cxdzyq1110/posture_recognition_CNN/projects/matlab/hog_svm/man+bike.png

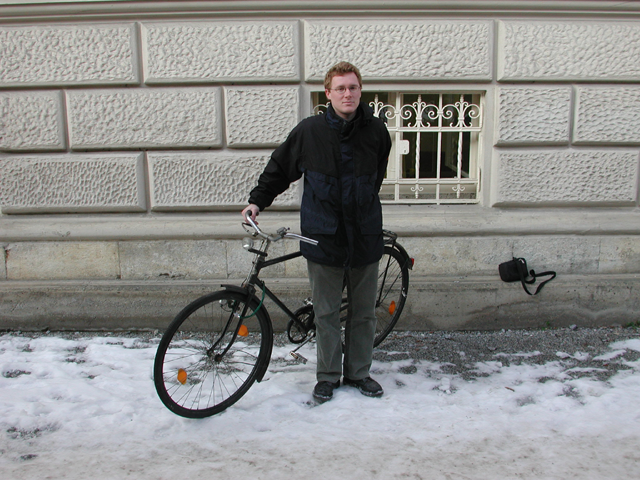
projects/matlab/hog_svm/man+bike.png
