cxdzyq1110/posture_recognition_CNN/projects/matlab/picture/wangjunkai/1.jpg

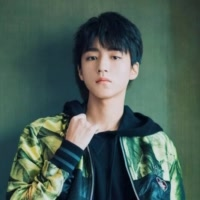
projects/matlab/picture/wangjunkai/1.jpg
