cxdzyq1110/posture_recognition_CNN/projects/zFPGA_DE10_NANO_SoC/01_altera_ip/soc_system/soc_system/synthesis/submodules/soc_system_mm_interconnect_0_router.sv

// (C) 2001-2014 Altera Corporation. All rights reserved.
// Your use of Altera Corporation's design tools, logic functions and other 
// software and tools, and its AMPP partner logic functions, and any output 
// files any of the foregoing (including device programming or simulation 
// files), and any associated documentation or information are expressly subject 
// to the terms and conditions of the Altera Program License Subscription 
// Agreement, Altera MegaCore Function License Agreement, or other applicable 
// license agreement, including, without limitation, that your use is for the 
// sole purpose of programming logic devices manufactured by Altera and sold by 
// Altera or its authorized distributors.  Please refer to the applicable 
// agreement for further details.



// Your use of Altera Corporation's design tools, logic functions and other 
// software and tools, and its AMPP partner logic functions, and any output 
// files any of the foregoing (including device programming or simulation 
// files), and any associated documentation or information are expressly subject 
// to the terms and conditions of the Altera Program License Subscription 
// Agreement, Altera MegaCore Function License Agreement, or other applicable 
// license agreement, including, without limitation, that your use is for the 
// sole purpose of programming logic devices manufactured by Altera and sold by 
// Altera or its authorized distributors.  Please refer to the applicable 
// agreement for further details.


// $Id: //acds/rel/14.0/ip/merlin/altera_merlin_router/altera_merlin_router.sv.terp#1 $
// $Revision: #1 $
// $Date: 2014/02/16 $
// $Author: swbranch $

// -------------------------------------------------------
// Merlin Router
//
// Asserts the appropriate one-hot encoded channel based on 
// either (a) the address or (b) the dest id. The DECODER_TYPE
// parameter controls this behaviour. 0 means address decoder,
// 1 means dest id decoder.
//
// In the case of (a), it also sets the destination id.
// -------------------------------------------------------

`timescale 1 ns / 1 ns

module soc_system_mm_interconnect_0_router_default_decode
  #(
     parameter DEFAULT_CHANNEL = 2,
               DEFAULT_WR_CHANNEL = -1,
               DEFAULT_RD_CHANNEL = -1,
               DEFAULT_DESTID = 0 
   )
  (output [91 - 89 : 0] default_destination_id,
   output [8-1 : 0] default_wr_channel,
   output [8-1 : 0] default_rd_channel,
   output [8-1 : 0] default_src_channel
  );

  assign default_destination_id = 
    DEFAULT_DESTID[91 - 89 : 0];

  generate begin : default_decode
    if (DEFAULT_CHANNEL == -1) begin
      assign default_src_channel = '0;
    end
    else begin
      assign default_src_channel = 8'b1 << DEFAULT_CHANNEL;
    end
  end
  endgenerate

  generate begin : default_decode_rw
    if (DEFAULT_RD_CHANNEL == -1) begin
      assign default_wr_channel = '0;
      assign default_rd_channel = '0;
    end
    else begin
      assign default_wr_channel = 8'b1 << DEFAULT_WR_CHANNEL;
      assign default_rd_channel = 8'b1 << DEFAULT_RD_CHANNEL;
    end
  end
  endgenerate

endmodule


module soc_system_mm_interconnect_0_router
(
    // -------------------
    // Clock & Reset
    // -------------------
    input clk,
    input reset,

    // -------------------
    // Command Sink (Input)
    // -------------------
    input                       sink_valid,
    input  [116-1 : 0]    sink_data,
    input                       sink_startofpacket,
    input                       sink_endofpacket,
    output                      sink_ready,

    // -------------------
    // Command Source (Output)
    // -------------------
    output                          src_valid,
    output reg [116-1    : 0] src_data,
    output reg [8-1 : 0] src_channel,
    output                          src_startofpacket,
    output                          src_endofpacket,
    input                           src_ready
);

    // -------------------------------------------------------
    // Local parameters and variables
    // -------------------------------------------------------
    localparam PKT_ADDR_H = 56;
    localparam PKT_ADDR_L = 36;
    localparam PKT_DEST_ID_H = 91;
    localparam PKT_DEST_ID_L = 89;
    localparam PKT_PROTECTION_H = 106;
    localparam PKT_PROTECTION_L = 104;
    localparam ST_DATA_W = 116;
    localparam ST_CHANNEL_W = 8;
    localparam DECODER_TYPE = 0;

    localparam PKT_TRANS_WRITE = 59;
    localparam PKT_TRANS_READ  = 60;

    localparam PKT_ADDR_W = PKT_ADDR_H-PKT_ADDR_L + 1;
    localparam PKT_DEST_ID_W = PKT_DEST_ID_H-PKT_DEST_ID_L + 1;



    // -------------------------------------------------------
    // Figure out the number of bits to mask off for each slave span
    // during address decoding
    // -------------------------------------------------------
    localparam PAD0 = log2ceil(64'h10000 - 64'h0); 
    localparam PAD1 = log2ceil(64'h40018 - 64'h40010); 
    localparam PAD2 = log2ceil(64'h40030 - 64'h40020); 
    localparam PAD3 = log2ceil(64'h41010 - 64'h41000); 
    localparam PAD4 = log2ceil(64'h42010 - 64'h42000); 
    localparam PAD5 = log2ceil(64'h43010 - 64'h43000); 
    localparam PAD6 = log2ceil(64'h44010 - 64'h44000); 
    localparam PAD7 = log2ceil(64'h49000 - 64'h48000); 
    // -------------------------------------------------------
    // Work out which address bits are significant based on the
    // address range of the slaves. If the required width is too
    // large or too small, we use the address field width instead.
    // -------------------------------------------------------
    localparam ADDR_RANGE = 64'h49000;
    localparam RANGE_ADDR_WIDTH = log2ceil(ADDR_RANGE);
    localparam OPTIMIZED_ADDR_H = (RANGE_ADDR_WIDTH > PKT_ADDR_W) ||
                                  (RANGE_ADDR_WIDTH == 0) ?
                                        PKT_ADDR_H :
                                        PKT_ADDR_L + RANGE_ADDR_WIDTH - 1;

    localparam RG = RANGE_ADDR_WIDTH-1;
    localparam REAL_ADDRESS_RANGE = OPTIMIZED_ADDR_H - PKT_ADDR_L;

      reg [PKT_ADDR_W-1 : 0] address;
      always @* begin
        address = {PKT_ADDR_W{1'b0}};
        address [REAL_ADDRESS_RANGE:0] = sink_data[OPTIMIZED_ADDR_H : PKT_ADDR_L];
      end   

    // -------------------------------------------------------
    // Pass almost everything through, untouched
    // -------------------------------------------------------
    assign sink_ready        = src_ready;
    assign src_valid         = sink_valid;
    assign src_startofpacket = sink_startofpacket;
    assign src_endofpacket   = sink_endofpacket;
    wire [PKT_DEST_ID_W-1:0] default_destid;
    wire [8-1 : 0] default_src_channel;




    // -------------------------------------------------------
    // Write and read transaction signals
    // -------------------------------------------------------
    wire read_transaction;
    assign read_transaction  = sink_data[PKT_TRANS_READ];


    soc_system_mm_interconnect_0_router_default_decode the_default_decode(
      .default_destination_id (default_destid),
      .default_wr_channel   (),
      .default_rd_channel   (),
      .default_src_channel  (default_src_channel)
    );

    always @* begin
        src_data    = sink_data;
        src_channel = default_src_channel;
        src_data[PKT_DEST_ID_H:PKT_DEST_ID_L] = default_destid;

        // --------------------------------------------------
        // Address Decoder
        // Sets the channel and destination ID based on the address
        // --------------------------------------------------

    // ( 0x0 .. 0x10000 )
    if ( {address[RG:PAD0],{PAD0{1'b0}}} == 19'h0   ) begin
            src_channel = 8'b00000100;
            src_data[PKT_DEST_ID_H:PKT_DEST_ID_L] = 0;
    end

    // ( 0x40010 .. 0x40018 )
    if ( {address[RG:PAD1],{PAD1{1'b0}}} == 19'h40010  && read_transaction  ) begin
            src_channel = 8'b00000001;
            src_data[PKT_DEST_ID_H:PKT_DEST_ID_L] = 6;
    end

    // ( 0x40020 .. 0x40030 )
    if ( {address[RG:PAD2],{PAD2{1'b0}}} == 19'h40020   ) begin
            src_channel = 8'b00000010;
            src_data[PKT_DEST_ID_H:PKT_DEST_ID_L] = 3;
    end

    // ( 0x41000 .. 0x41010 )
    if ( {address[RG:PAD3],{PAD3{1'b0}}} == 19'h41000   ) begin
            src_channel = 8'b00001000;
            src_data[PKT_DEST_ID_H:PKT_DEST_ID_L] = 2;
    end

    // ( 0x42000 .. 0x42010 )
    if ( {address[RG:PAD4],{PAD4{1'b0}}} == 19'h42000  && read_transaction  ) begin
            src_channel = 8'b00010000;
            src_data[PKT_DEST_ID_H:PKT_DEST_ID_L] = 1;
    end

    // ( 0x43000 .. 0x43010 )
    if ( {address[RG:PAD5],{PAD5{1'b0}}} == 19'h43000  && read_transaction  ) begin
            src_channel = 8'b00100000;
            src_data[PKT_DEST_ID_H:PKT_DEST_ID_L] = 7;
    end

    // ( 0x44000 .. 0x44010 )
    if ( {address[RG:PAD6],{PAD6{1'b0}}} == 19'h44000   ) begin
            src_channel = 8'b01000000;
            src_data[PKT_DEST_ID_H:PKT_DEST_ID_L] = 4;
    end

    // ( 0x48000 .. 0x49000 )
    if ( {address[RG:PAD7],{PAD7{1'b0}}} == 19'h48000   ) begin
            src_channel = 8'b10000000;
            src_data[PKT_DEST_ID_H:PKT_DEST_ID_L] = 5;
    end

end


    // --------------------------------------------------
    // Ceil(log2()) function
    // --------------------------------------------------
    function integer log2ceil;
        input reg[65:0] val;
        reg [65:0] i;

        begin
            i = 1;
            log2ceil = 0;

            while (i < val) begin
                log2ceil = log2ceil + 1;
                i = i << 1;
            end
        end
    endfunction

endmodule
