cxdzyq1110/posture_recognition_CNN/projects/zFPGA_DE10_NANO_SoC/08_quartus/hps_isw_handoff/soc_system_hps_0/sequencer.c

/*
* Copyright Altera Corporation (C) 2012-2014. All rights reserved
*
* SPDX-License-Identifier:  BSD-3-Clause
*
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
* THIS SOFTWARE IS PROVIDED BY THE COPYRIGHT HOLDERS AND CONTRIBUTORS "AS IS" AND
* ANY EXPRESS OR IMPLIED WARRANTIES, INCLUDING, BUT NOT LIMITED TO, THE IMPLIED
* WARRANTIES OF MERCHANTABILITY AND FITNESS FOR A PARTICULAR PURPOSE ARE
* DISCLAIMED. IN NO EVENT SHALL ALTERA CORPORATION BE LIABLE FOR ANY
* DIRECT, INDIRECT, INCIDENTAL, SPECIAL, EXEMPLARY, OR CONSEQUENTIAL DAMAGES
* (INCLUDING, BUT NOT LIMITED TO, PROCUREMENT OF SUBSTITUTE GOODS OR SERVICES;
* LOSS OF USE, DATA, OR PROFITS; OR BUSINESS INTERRUPTION) HOWEVER CAUSED AND
* ON ANY THEORY OF LIABILITY, WHETHER IN CONTRACT, STRICT LIABILITY, OR TORT
* (INCLUDING NEGLIGENCE OR OTHERWISE) ARISING IN ANY WAY OUT OF THE USE OF THIS
* SOFTWARE, EVEN IF ADVISED OF THE POSSIBILITY OF SUCH DAMAGE.
*/


#include "sequencer_defines.h"

#include "alt_types.h"
#include "system.h"
#if HPS_HW
#include "sdram_io.h"
#else
#include "io.h"
#endif
#include "sequencer.h"
#include "tclrpt.h"
#include "sequencer_auto.h"

#if HHP_HPS_SIMULATION
#include "hps_controller.h"
#endif


/******************************************************************************
 ******************************************************************************
 ** NOTE: Special Rules for Globale Variables                                **
 **                                                                          **
 ** All global variables that are explicitly initialized (including          **
 ** explicitly initialized to zero), are only initialized once, during       **
 ** configuration time, and not again on reset.  This means that they        **
 ** preserve their current contents across resets, which is needed for some  **
 ** special cases involving communication with external modules.  In         **
 ** addition, this avoids paying the price to have the memory initialized,   **
 ** even for zeroed data, provided it is explicitly set to zero in the code, **
 ** and doesn't rely on implicit initialization.                             **
 ******************************************************************************
 ******************************************************************************/


#if ARRIAV
// Temporary workaround to place the initial stack pointer at a safe offset from end
#define STRINGIFY(s)		STRINGIFY_STR(s)
#define STRINGIFY_STR(s)	#s
asm(".global __alt_stack_pointer");
asm("__alt_stack_pointer = " STRINGIFY(STACK_POINTER));
#endif

#if CYCLONEV
// Temporary workaround to place the initial stack pointer at a safe offset from end
#define STRINGIFY(s)		STRINGIFY_STR(s)
#define STRINGIFY_STR(s)	#s
asm(".global __alt_stack_pointer");
asm("__alt_stack_pointer = " STRINGIFY(STACK_POINTER));
#endif

#if ENABLE_PRINTF_LOG
#include <stdio.h>
#include <string.h>

typedef struct {
	alt_u32 v;
	alt_u32 p;
	alt_u32 d;
	alt_u32 ps;
} dqs_pos_t;

/*
The parameters that were previously here are now supplied by generation, until the new data manager is working.
*/

struct {
	const char *stage;

	alt_u32 vfifo_idx;

	dqs_pos_t gwrite_pos[RW_MGR_MEM_IF_WRITE_DQS_WIDTH];

	dqs_pos_t dqs_enable_left_edge[RW_MGR_MEM_IF_READ_DQS_WIDTH];
	dqs_pos_t dqs_enable_right_edge[RW_MGR_MEM_IF_READ_DQS_WIDTH];
	dqs_pos_t dqs_enable_mid[RW_MGR_MEM_IF_READ_DQS_WIDTH];

	dqs_pos_t dqs_wlevel_left_edge[RW_MGR_MEM_IF_WRITE_DQS_WIDTH];
	dqs_pos_t dqs_wlevel_right_edge[RW_MGR_MEM_IF_WRITE_DQS_WIDTH];
	dqs_pos_t dqs_wlevel_mid[RW_MGR_MEM_IF_WRITE_DQS_WIDTH];

	alt_32 dq_read_left_edge[RW_MGR_MEM_IF_READ_DQS_WIDTH][RW_MGR_MEM_DQ_PER_READ_DQS];
	alt_32 dq_read_right_edge[RW_MGR_MEM_IF_READ_DQS_WIDTH][RW_MGR_MEM_DQ_PER_READ_DQS];
	alt_32 dq_write_left_edge[RW_MGR_MEM_IF_WRITE_DQS_WIDTH][RW_MGR_MEM_DQ_PER_READ_DQS];
	alt_32 dq_write_right_edge[RW_MGR_MEM_IF_WRITE_DQS_WIDTH][RW_MGR_MEM_DQ_PER_READ_DQS];
	alt_32 dm_left_edge[RW_MGR_MEM_IF_WRITE_DQS_WIDTH][RW_MGR_NUM_DM_PER_WRITE_GROUP];
	alt_32 dm_right_edge[RW_MGR_MEM_IF_WRITE_DQS_WIDTH][RW_MGR_NUM_DM_PER_WRITE_GROUP];
} bfm_gbl;

#endif

#if HPS_HW
#include <sdram.h>
#endif // HPS_HW

#if BFM_MODE
#include <stdio.h>

// DPI access function via library
extern long long get_sim_time(void);

typedef struct {
	alt_u32 v;
	alt_u32 p;
	alt_u32 d;
	alt_u32 ps;
} dqs_pos_t;

/*
The parameters that were previously here are now supplied by generation, until the new data manager is working.
*/

struct {
	FILE *outfp;
	int bfm_skip_guaranteed_write;
	int trk_sample_count;
	int trk_long_idle_updates;
	int lfifo_margin;
	const char *stage;

	alt_u32 vfifo_idx;

	dqs_pos_t gwrite_pos[RW_MGR_MEM_IF_WRITE_DQS_WIDTH];
	
	dqs_pos_t dqs_enable_left_edge[RW_MGR_MEM_IF_READ_DQS_WIDTH];
	dqs_pos_t dqs_enable_right_edge[RW_MGR_MEM_IF_READ_DQS_WIDTH];
	dqs_pos_t dqs_enable_mid[RW_MGR_MEM_IF_READ_DQS_WIDTH];

	dqs_pos_t dqs_wlevel_left_edge[RW_MGR_MEM_IF_WRITE_DQS_WIDTH];
	dqs_pos_t dqs_wlevel_right_edge[RW_MGR_MEM_IF_WRITE_DQS_WIDTH];
	dqs_pos_t dqs_wlevel_mid[RW_MGR_MEM_IF_WRITE_DQS_WIDTH];

	alt_32 dq_read_left_edge[RW_MGR_MEM_IF_READ_DQS_WIDTH][RW_MGR_MEM_DQ_PER_READ_DQS];
	alt_32 dq_read_right_edge[RW_MGR_MEM_IF_READ_DQS_WIDTH][RW_MGR_MEM_DQ_PER_READ_DQS];
	alt_32 dq_write_left_edge[RW_MGR_MEM_IF_WRITE_DQS_WIDTH][RW_MGR_MEM_DQ_PER_WRITE_DQS];
	alt_32 dq_write_right_edge[RW_MGR_MEM_IF_WRITE_DQS_WIDTH][RW_MGR_MEM_DQ_PER_WRITE_DQS];
	alt_32 dm_left_edge[RW_MGR_MEM_IF_WRITE_DQS_WIDTH][RW_MGR_NUM_DM_PER_WRITE_GROUP];
	alt_32 dm_right_edge[RW_MGR_MEM_IF_WRITE_DQS_WIDTH][RW_MGR_NUM_DM_PER_WRITE_GROUP];
} bfm_gbl;


#endif

#if ENABLE_TCL_DEBUG
debug_data_t my_debug_data;
#endif

#define NEWVERSION_RDDESKEW 1
#define NEWVERSION_WRDESKEW 1
#define NEWVERSION_GW 1
#define NEWVERSION_WL 1
#define NEWVERSION_DQSEN 1

// Just to make the debugging code more uniform
#ifndef RW_MGR_MEM_NUMBER_OF_CS_PER_DIMM
#define RW_MGR_MEM_NUMBER_OF_CS_PER_DIMM 0
#endif

#if HALF_RATE
#define HALF_RATE_MODE 1
#else
#define HALF_RATE_MODE 0
#endif

#if QUARTER_RATE
#define QUARTER_RATE_MODE 1
#else
#define QUARTER_RATE_MODE 0
#endif
#define DELTA_D 1

// case:56390
// VFIFO_CONTROL_WIDTH_PER_DQS is the number of VFIFOs actually instantiated per DQS. This is always one except:
// AV QDRII where it is 2 for x18 and x18w2, and 4 for x36 and x36w2
// RLDRAMII x36 and x36w2 where it is 2.
// In 12.0sp1 we set this to 4 for all of the special cases above to keep it simple.
// In 12.0sp2 or 12.1 this should get moved to generation and unified with the same constant used in the phy mgr

#define VFIFO_CONTROL_WIDTH_PER_DQS 1

#if ARRIAV

#if QDRII 
 #if RW_MGR_MEM_DQ_PER_READ_DQS > 9
  #undef VFIFO_CONTROL_WIDTH_PER_DQS
  #define VFIFO_CONTROL_WIDTH_PER_DQS 4
 #endif
#endif // protocol check

#if RLDRAMII
 #if RW_MGR_MEM_DQ_PER_READ_DQS > 9
  #undef VFIFO_CONTROL_WIDTH_PER_DQS
  #define VFIFO_CONTROL_WIDTH_PER_DQS 2
 #endif
#endif // protocol check

#endif // family check

// In order to reduce ROM size, most of the selectable calibration steps are
// decided at compile time based on the user's calibration mode selection,
// as captured by the STATIC_CALIB_STEPS selection below.
//
// However, to support simulation-time selection of fast simulation mode, where
// we skip everything except the bare minimum, we need a few of the steps to
// be dynamic.  In those cases, we either use the DYNAMIC_CALIB_STEPS for the
// check, which is based on the rtl-supplied value, or we dynamically compute the
// value to use based on the dynamically-chosen calibration mode

#if QDRII
#define BTFLD_FMT "%llx"
#else
#define BTFLD_FMT "%lx"
#endif

#if BFM_MODE // ~~~~~~~~~~~~~~~~~~~~~~~~~~~~~~~~~~~~~~~~~~~~~~~~~~~~~~~~~~~~~~~~~~~~~~~~


// TODO: should make this configurable; could even have it read from config file or env at startup
#define DLEVEL 2
// space around comma is required for varargs macro to remove comma if args is empty
#define DPRINT(level, fmt, args...) 	if (DLEVEL >= (level)) printf("[%lld] SEQ.C: " fmt "\n" , get_sim_time(), ## args)
#define IPRINT(fmt, args...) 	printf("[%lld] SEQ.C: " fmt "\n" , get_sim_time(), ## args)
#define BFM_GBL_SET(field,value)	bfm_gbl.field = value
#define BFM_GBL_GET(field)		bfm_gbl.field
#define BFM_STAGE(label)		BFM_GBL_SET(stage,label)
#define BFM_INC_VFIFO			bfm_gbl.vfifo_idx = (bfm_gbl.vfifo_idx + 1) % VFIFO_SIZE
#define COV(label)			getpid() /* no-op marker for coverage */

#elif ENABLE_PRINTF_LOG // ~~~~~~~~~~~~~~~~~~~~~~~~~~~~~~~~~~~~~~~~~~~~~~~~~~~~~~~~~~~~~~

#define DLEVEL 2

void wait_printf_queue()
{
	alt_u32 next_entry;

	while (debug_printf_output->count == PRINTF_READ_BUFFER_FIFO_WORDS || debug_printf_output->slave_lock != 0)
	{}

	debug_printf_output->master_lock = 1;
	next_entry = (debug_printf_output->head + debug_printf_output->count) % PRINTF_READ_BUFFER_FIFO_WORDS;
	strcpy((char*)(&(debug_printf_output->read_buffer[next_entry])), (char*)(debug_printf_output->active_word));
	debug_printf_output->count++;
	debug_printf_output->master_lock = 0;
}
#define DPRINT(level, fmt, args...) \
	if (DLEVEL >= (level)) { \
		snprintf((char*)(debug_printf_output->active_word), PRINTF_READ_BUFFER_SIZE*4, "DEBUG:" fmt, ## args); \
		wait_printf_queue(); \
	}
#define IPRINT(fmt, args...) \
		snprintf((char*)(debug_printf_output->active_word), PRINTF_READ_BUFFER_SIZE*4, "INFO:" fmt, ## args); \
		wait_printf_queue();

#define BFM_GBL_SET(field,value)	bfm_gbl.field = value
#define BFM_GBL_GET(field)		bfm_gbl.field
#define BFM_STAGE(label)		BFM_GBL_SET(stage,label)
#define BFM_INC_VFIFO			bfm_gbl.vfifo_idx = (bfm_gbl.vfifo_idx + 1) % VFIFO_SIZE
#define COV(label)

#elif HPS_HW // ~~~~~~~~~~~~~~~~~~~~~~~~~~~~~~~~~~~~~~~~~~~~~~~~~~~~~~~~~~~~~~~~~~~~~~~~~

// For HPS running on actual hardware

#define DLEVEL 0
#ifdef HPS_HW_SERIAL_SUPPORT
// space around comma is required for varargs macro to remove comma if args is empty
#define DPRINT(level, fmt, args...) 	if (DLEVEL >= (level)) printf("SEQ.C: " fmt "\n" , ## args)
#define IPRINT(fmt, args...) 	        printf("SEQ.C: " fmt "\n" , ## args)
#if RUNTIME_CAL_REPORT
#define RPRINT(fmt, args...)            printf("SEQ.C: " fmt "\n" , ## args)
#endif 
#else
#define DPRINT(level, fmt, args...)
#define IPRINT(fmt, args...)
#endif
#define BFM_GBL_SET(field,value)
#define BFM_GBL_GET(field) 		((long unsigned int)0)
#define BFM_STAGE(stage)	
#define BFM_INC_VFIFO
#define COV(label)

#else // ~~~~~~~~~~~~~~~~~~~~~~~~~~~~~~~~~~~~~~~~~~~~~-----------------------------------

// Default mode
#define DPRINT(level, fmt, args...) 
#define IPRINT(fmt, args...)
#define BFM_GBL_SET(field,value)
#define BFM_GBL_GET(field) 0
#define BFM_STAGE(stage)	
#define BFM_INC_VFIFO
#define COV(label)

#endif // ~~~~~~~~~~~~~~~~~~~~~~~~~~~~~~~~~~~~~~~~~~~~~----------------------------------

#if BFM_MODE
#define TRACE_FUNC(fmt, args...) DPRINT(1, "%s[%ld]: " fmt, __func__, __LINE__ , ## args)
#else
#define TRACE_FUNC(fmt, args...) DPRINT(1, "%s[%d]: " fmt, __func__, __LINE__ , ## args)
#endif

#if BFM_MODE
// In BFM mode, we do full calibration as for real-rtl
#define DYNAMIC_CALIB_STEPS STATIC_CALIB_STEPS
#else
#define DYNAMIC_CALIB_STEPS (dyn_calib_steps)
#endif

#if STATIC_SIM_FILESET
#define STATIC_IN_RTL_SIM CALIB_IN_RTL_SIM
#else
#define STATIC_IN_RTL_SIM 0
#endif

#if STATIC_SKIP_MEM_INIT
#define STATIC_SKIP_DELAY_LOOPS CALIB_SKIP_DELAY_LOOPS
#else
#define STATIC_SKIP_DELAY_LOOPS 0
#endif

#if STATIC_FULL_CALIBRATION
#define STATIC_CALIB_STEPS (STATIC_IN_RTL_SIM | CALIB_SKIP_FULL_TEST | STATIC_SKIP_DELAY_LOOPS)
#elif STATIC_QUICK_CALIBRATION
#define STATIC_CALIB_STEPS (STATIC_IN_RTL_SIM | CALIB_SKIP_FULL_TEST | CALIB_SKIP_WRITES | CALIB_SKIP_DELAY_SWEEPS | CALIB_SKIP_ALL_BITS_CHK | STATIC_SKIP_DELAY_LOOPS)
#elif STATIC_SKIP_CALIBRATION
#define STATIC_CALIB_STEPS (STATIC_IN_RTL_SIM | CALIB_SKIP_FULL_TEST | CALIB_SKIP_WRITES | CALIB_SKIP_WLEVEL | CALIB_SKIP_LFIFO | CALIB_SKIP_VFIFO | CALIB_SKIP_DELAY_SWEEPS | CALIB_SKIP_ALL_BITS_CHK | STATIC_SKIP_DELAY_LOOPS)
#else
#undef STATIC_CALIB_STEPS
// This should force an error
#endif

// calibration steps requested by the rtl
alt_u16 dyn_calib_steps = 0;

// To make CALIB_SKIP_DELAY_LOOPS a dynamic conditional option
// instead of static, we use boolean logic to select between
// non-skip and skip values
//
// The mask is set to include all bits when not-skipping, but is
// zero when skipping

alt_u16 skip_delay_mask = 0;	// mask off bits when skipping/not-skipping

#define SKIP_DELAY_LOOP_VALUE_OR_ZERO(non_skip_value) \
	((non_skip_value) & skip_delay_mask)


// TODO: The skip group strategy is completely missing

gbl_t *gbl = 0;
param_t *param = 0;

alt_u32 curr_shadow_reg = 0;

#if ENABLE_DELAY_CHAIN_WRITE
alt_u32 vfifo_settings[RW_MGR_MEM_IF_READ_DQS_WIDTH];
#endif // ENABLE_DELAY_CHAIN_WRITE

#if ENABLE_NON_DESTRUCTIVE_CALIB
// Technically, the use of these variables could be separated from ENABLE_NON_DESTRUCTIVE_CALIB
// but currently they are part of a single feature which is not fully validated, so we're keeping
// them together

// These variables can be modified by external rtl modules, and hence are "volatile"
volatile alt_u32 no_init = 0;
volatile alt_u32 abort_cal = 0;
#endif

alt_u32 rw_mgr_mem_calibrate_write_test (alt_u32 rank_bgn, alt_u32 write_group, alt_u32 use_dm, alt_u32 all_correct, t_btfld *bit_chk, alt_u32 all_ranks);

#if ENABLE_BRINGUP_DEBUGGING

#define DI_BUFFER_DEBUG_SIZE   64

alt_u8 di_buf_gbl[DI_BUFFER_DEBUG_SIZE*4] = {0};

void load_di_buf_gbl(void)
{
	int i;
	int j;

	for (i = 0; i < DI_BUFFER_DEBUG_SIZE; i++) {
		alt_u32 val = IORD_32DIRECT(RW_MGR_DI_BASE + i*4, 0);
		for (j = 0; j < 4; j++) {
			alt_u8 byte = (val >> (8*j)) & 0xff;
			di_buf_gbl[i*4 + j] = byte;
		}
	}
}

#endif	/* ENABLE_BRINGUP_DEBUGGING */


#if ENABLE_DQSEN_SWEEP
void init_di_buffer(void)
{
	alt_u32 i;

	debug_data->di_report.flags = 0;
	debug_data->di_report.cur_samples = 0;

	for (i = 0; i < NUM_DI_SAMPLE; i++)
	{
		debug_data->di_report.di_buffer[i].bit_chk = 0;
		debug_data->di_report.di_buffer[i].delay = 0;
		debug_data->di_report.di_buffer[i].d = 0;
		debug_data->di_report.di_buffer[i].v = 0;
		debug_data->di_report.di_buffer[i].p = 0;
		debug_data->di_report.di_buffer[i].di_buffer_0a = 0;
		debug_data->di_report.di_buffer[i].di_buffer_0b = 0;
		debug_data->di_report.di_buffer[i].di_buffer_1a = 0;
		debug_data->di_report.di_buffer[i].di_buffer_1b = 0;
		debug_data->di_report.di_buffer[i].di_buffer_2a = 0;
		debug_data->di_report.di_buffer[i].di_buffer_2b = 0;
		debug_data->di_report.di_buffer[i].di_buffer_3a = 0;
		debug_data->di_report.di_buffer[i].di_buffer_3b = 0;
		debug_data->di_report.di_buffer[i].di_buffer_4a = 0;
		debug_data->di_report.di_buffer[i].di_buffer_4b = 0;
	}
}

inline void flag_di_buffer_ready()
{
	debug_data->di_report.flags |= DI_REPORT_FLAGS_READY;
}

inline void flag_di_buffer_done()
{
	debug_data->di_report.flags |= DI_REPORT_FLAGS_READY;
	debug_data->di_report.flags |= DI_REPORT_FLAGS_DONE;
}

void wait_di_buffer(void)
{
	if (debug_data->di_report.cur_samples == NUM_DI_SAMPLE)
	{
		flag_di_buffer_ready();
		while (debug_data->di_report.cur_samples != 0)
		{
		}
		debug_data->di_report.flags = 0;
	}
}

void sample_di_data(alt_u32 bit_chk, alt_u32 delay, alt_u32 d, alt_u32 v, alt_u32 p)
{
	alt_u32 k;
	alt_u32 di_status_word;
	alt_u32 di_word_avail;
	alt_u32 di_write_to_read_ratio;
	alt_u32 di_write_to_read_ratio_2_exp;

	wait_di_buffer();

	k = debug_data->di_report.cur_samples;

	debug_data->di_report.di_buffer[k].bit_chk = bit_chk;
	debug_data->di_report.di_buffer[k].delay = delay;
	debug_data->di_report.di_buffer[k].d = d;
	debug_data->di_report.di_buffer[k].v = v;
	debug_data->di_report.di_buffer[k].p = p;

	di_status_word = IORD_32DIRECT(BASE_RW_MGR + 8, 0);
	di_word_avail = di_status_word & 0x0000FFFF;
	di_write_to_read_ratio = (di_status_word & 0x00FF0000) >> 16;
	di_write_to_read_ratio_2_exp = (di_status_word & 0xFF000000) >> 24;

	debug_data->di_report.di_buffer[k].di_buffer_0a = IORD_32DIRECT(BASE_RW_MGR + 16 + 0*4, 0);
	debug_data->di_report.di_buffer[k].di_buffer_0b = IORD_32DIRECT(BASE_RW_MGR + 16 + 1*4, 0);
	debug_data->di_report.di_buffer[k].di_buffer_1a = IORD_32DIRECT(BASE_RW_MGR + 16 + 2*4, 0);
	debug_data->di_report.di_buffer[k].di_buffer_1b = IORD_32DIRECT(BASE_RW_MGR + 16 + 3*4, 0);
	debug_data->di_report.di_buffer[k].di_buffer_2a = IORD_32DIRECT(BASE_RW_MGR + 16 + 4*4, 0);
	debug_data->di_report.di_buffer[k].di_buffer_2b = IORD_32DIRECT(BASE_RW_MGR + 16 + 5*4, 0);
	debug_data->di_report.di_buffer[k].di_buffer_3a = IORD_32DIRECT(BASE_RW_MGR + 16 + 6*4, 0);
	debug_data->di_report.di_buffer[k].di_buffer_3b = IORD_32DIRECT(BASE_RW_MGR + 16 + 7*4, 0);
	debug_data->di_report.di_buffer[k].di_buffer_4a = IORD_32DIRECT(BASE_RW_MGR + 16 + 8*4, 0);
	debug_data->di_report.di_buffer[k].di_buffer_4b = IORD_32DIRECT(BASE_RW_MGR + 16 + 9*4, 0);

	debug_data->di_report.cur_samples = debug_data->di_report.cur_samples + 1;
}
#endif

// This (TEST_SIZE) is used to test handling of large roms, to make
// sure we are sizing things correctly
// Note, the initialized data takes up twice the space in rom, since
// there needs to be a copy with the initial value and a copy that is
// written too, since on soft-reset, it needs to have the initial values
// without reloading the memory from external sources

// #define TEST_SIZE	(6*1024)

#ifdef TEST_SIZE

#define PRE_POST_TEST_SIZE 3

unsigned int pre_test_size_mem[PRE_POST_TEST_SIZE] = { 1, 2, 3};

unsigned int test_size_mem[TEST_SIZE/sizeof(unsigned int)] = { 100, 200, 300 };

unsigned int post_test_size_mem[PRE_POST_TEST_SIZE] = {10, 20, 30};

void write_test_mem(void)
{
	int i;

	for (i = 0; i < PRE_POST_TEST_SIZE; i++) {
		pre_test_size_mem[i] = (i+1)*10;
		post_test_size_mem[i] = (i+1);
	}
	
	for (i = 0; i < sizeof(test_size_mem)/sizeof(unsigned int); i++) {
		test_size_mem[i] = i;
	}
	
}

int check_test_mem(int start)
{
	int i;

	for (i = 0; i < PRE_POST_TEST_SIZE; i++) {
		if (start) {
			if (pre_test_size_mem[i] != (i+1)) {
				return 0;
			}
			if (post_test_size_mem[i] != (i+1)*10) {
				return 0;
			}
		} else {
			if (pre_test_size_mem[i] != (i+1)*10) {
				return 0;
			}
			if (post_test_size_mem[i] != (i+1)) {
				return 0;
			}
		}
	}
		
	for (i = 0; i < sizeof(test_size_mem)/sizeof(unsigned int); i++) {
		if (start) {
			if (i < 3) {
				if (test_size_mem[i] != (i+1)*100) {
					return 0;
				}
			} else {
				if (test_size_mem[i] != 0) {
					return 0;
				}
			}
		} else {
			if (test_size_mem[i] != i) {
				return 0;
			}
		}
	}

	return 1;
}

#endif // TEST_SIZE

static void set_failing_group_stage(alt_u32 group, alt_u32 stage, alt_u32 substage)
{
	ALTERA_ASSERT(group < RW_MGR_MEM_IF_WRITE_DQS_WIDTH);

	// Only set the global stage if there was not been any other failing group
	if (gbl->error_stage == CAL_STAGE_NIL)
	{
		gbl->error_substage = substage;
		gbl->error_stage = stage;
		gbl->error_group = group;
		TCLRPT_SET(debug_summary_report->error_sub_stage, substage);
		TCLRPT_SET(debug_summary_report->error_stage, stage);
		TCLRPT_SET(debug_summary_report->error_group, group);

	}

	// Always set the group specific errors
	TCLRPT_SET(debug_cal_report->cal_status_per_group[curr_shadow_reg][group].error_stage, stage);
	TCLRPT_SET(debug_cal_report->cal_status_per_group[curr_shadow_reg][group].error_sub_stage, substage);

}

static inline void reg_file_set_group(alt_u32 set_group)
{
	// Read the current group and stage
	alt_u32 cur_stage_group = IORD_32DIRECT (REG_FILE_CUR_STAGE, 0);

	// Clear the group
	cur_stage_group &= 0x0000FFFF;

	// Set the group
	cur_stage_group |= (set_group << 16);

	// Write the data back
	IOWR_32DIRECT (REG_FILE_CUR_STAGE, 0, cur_stage_group);
}

static inline void reg_file_set_stage(alt_u32 set_stage)
{
	// Read the current group and stage
	alt_u32 cur_stage_group = IORD_32DIRECT (REG_FILE_CUR_STAGE, 0);

	// Clear the stage and substage
	cur_stage_group &= 0xFFFF0000;

	// Set the stage
	cur_stage_group |= (set_stage & 0x000000FF);

	// Write the data back
	IOWR_32DIRECT (REG_FILE_CUR_STAGE, 0, cur_stage_group);
}

static inline void reg_file_set_sub_stage(alt_u32 set_sub_stage)
{
	// Read the current group and stage
	alt_u32 cur_stage_group = IORD_32DIRECT (REG_FILE_CUR_STAGE, 0);

	// Clear the substage
	cur_stage_group &= 0xFFFF00FF;

	// Set the sub stage
	cur_stage_group |= ((set_sub_stage << 8) & 0x0000FF00);

	// Write the data back
	IOWR_32DIRECT (REG_FILE_CUR_STAGE, 0, cur_stage_group);
}

static inline alt_u32 is_write_group_enabled_for_dm(alt_u32 write_group)
{
#if DM_PINS_ENABLED
 #if RLDRAMII
	alt_32 decrement_counter = write_group + 1;

	while (decrement_counter > 0)
	{
		decrement_counter -= RW_MGR_MEM_IF_WRITE_DQS_WIDTH/RW_MGR_MEM_DATA_MASK_WIDTH;
	}

	if (decrement_counter == 0)
	{
		return 1;
	}
	else
	{
		return 0;
	}
 #else
	return 1;
 #endif
#else
	return 0;
#endif
}

static inline void select_curr_shadow_reg_using_rank(alt_u32 rank)
{
#if USE_SHADOW_REGS
	//USER Map the rank to its shadow reg and set the global variable
	curr_shadow_reg = (rank >> (NUM_RANKS_PER_SHADOW_REG - 1));
#endif
}

void initialize(void)
{
	TRACE_FUNC();

	//USER calibration has control over path to memory 

#if HARD_PHY
	// In Hard PHY this is a 2-bit control:
	// 0: AFI Mux Select
	// 1: DDIO Mux Select
	IOWR_32DIRECT (PHY_MGR_MUX_SEL, 0, 0x3);
#else
	IOWR_32DIRECT (PHY_MGR_MUX_SEL, 0, 1);
#endif

	//USER memory clock is not stable we begin initialization 

	IOWR_32DIRECT (PHY_MGR_RESET_MEM_STBL, 0, 0);

	//USER calibration status all set to zero 

	IOWR_32DIRECT (PHY_MGR_CAL_STATUS, 0, 0);
	IOWR_32DIRECT (PHY_MGR_CAL_DEBUG_INFO, 0, 0);

	if (((DYNAMIC_CALIB_STEPS) & CALIB_SKIP_ALL) != CALIB_SKIP_ALL) {
		param->read_correct_mask_vg  = ((t_btfld)1 << (RW_MGR_MEM_DQ_PER_READ_DQS / RW_MGR_MEM_VIRTUAL_GROUPS_PER_READ_DQS)) - 1;
		param->write_correct_mask_vg = ((t_btfld)1 << (RW_MGR_MEM_DQ_PER_READ_DQS / RW_MGR_MEM_VIRTUAL_GROUPS_PER_READ_DQS)) - 1;
		param->read_correct_mask     = ((t_btfld)1 << RW_MGR_MEM_DQ_PER_READ_DQS) - 1;
		param->write_correct_mask    = ((t_btfld)1 << RW_MGR_MEM_DQ_PER_WRITE_DQS) - 1;
		param->dm_correct_mask       = ((t_btfld)1 << (RW_MGR_MEM_DATA_WIDTH / RW_MGR_MEM_DATA_MASK_WIDTH)) - 1;
	}
}


#if MRS_MIRROR_PING_PONG_ATSO
// This code is specific to the ATSO setup.  There are two ways to set
// the cs/odt mask:
// 1. the normal way (set_rank_and_odt_mask)
//  This method will be used in general.  The behavior will be to unmask
//  BOTH CS (i.e. broadcast to both sides as if calibrating one large interface).
// 2. this function
//  This method will be used for MRS settings only.  This allows us to do settings
//  on a per-side basis.  This is needed because Slot 1 Rank 1 needs a mirrored MRS.
// This function is specific to our setup ONLY.
void set_rank_and_odt_mask_for_ping_pong_atso(alt_u32 side, alt_u32 odt_mode)
{
	alt_u32 odt_mask_0 = 0;
	alt_u32 odt_mask_1 = 0;
	alt_u32 cs_and_odt_mask;
	
	if(odt_mode == RW_MGR_ODT_MODE_READ_WRITE)
	{
		//USER 1 Rank
		//USER Read: ODT = 0
		//USER Write: ODT = 1
		odt_mask_0 = 0x0;
		odt_mask_1 = 0x1;
	}
	else
	{
		odt_mask_0 = 0x0;
		odt_mask_1 = 0x0;
	}

	cs_and_odt_mask = 
		(0xFF & ~(1 << side)) |
		((0xFF & odt_mask_0) << 8) |
		((0xFF & odt_mask_1) << 16);

	IOWR_32DIRECT (RW_MGR_SET_CS_AND_ODT_MASK, 0, cs_and_odt_mask);
}
#endif

#if DDR3
void set_rank_and_odt_mask(alt_u32 rank, alt_u32 odt_mode)
{
	alt_u32 odt_mask_0 = 0;
	alt_u32 odt_mask_1 = 0;
	alt_u32 cs_and_odt_mask;
	
	if(odt_mode == RW_MGR_ODT_MODE_READ_WRITE)
	{
#if USE_SHADOW_REGS	
		alt_u32 rank_one_hot = (0xFF & (1 << rank));
		select_curr_shadow_reg_using_rank(rank);
	
		//USER Assert afi_rrank and afi_wrank. These signals ultimately drive
		//USER the read/write rank select signals which select the shadow register.
		IOWR_32DIRECT (RW_MGR_SET_ACTIVE_RANK, 0, rank_one_hot);
#endif	

		if ( LRDIMM ) {
			// USER LRDIMMs have two cases to consider: single-slot and dual-slot.
			// USER In single-slot, assert ODT for write only.
			// USER In dual-slot, assert ODT for both slots for write,
			// USER and on the opposite slot only for reads.
			// USER
			// USER Further complicating this is that both DIMMs have either 1 or 2 ODT
			// USER inputs, which do the same thing (only one is actually required).
			if ((RW_MGR_MEM_CHIP_SELECT_WIDTH/RW_MGR_MEM_NUMBER_OF_CS_PER_DIMM) == 1) {
				// USER Single-slot case
				if (RW_MGR_MEM_ODT_WIDTH == 1) {
					// USER Read = 0, Write = 1
					odt_mask_0 = 0x0;
					odt_mask_1 = 0x1;
				} else if (RW_MGR_MEM_ODT_WIDTH == 2) {
					// USER Read = 00, Write = 11
					odt_mask_0 = 0x0;
					odt_mask_1 = 0x3;
				}
			} else if ((RW_MGR_MEM_CHIP_SELECT_WIDTH/RW_MGR_MEM_NUMBER_OF_CS_PER_DIMM) == 2) {
				// USER Dual-slot case
				if (RW_MGR_MEM_ODT_WIDTH == 2) {
					// USER Read: asserted for opposite slot, Write: asserted for both
					odt_mask_0 = (rank < 2) ? 0x2 : 0x1;
					odt_mask_1 = 0x3;
				} else if (RW_MGR_MEM_ODT_WIDTH == 4) {
					// USER Read: asserted for opposite slot, Write: asserted for both
					odt_mask_0 = (rank < 2) ? 0xC : 0x3;
					odt_mask_1 = 0xF;
				}
			}
		} else if(RW_MGR_MEM_NUMBER_OF_RANKS == 1) { 
			//USER 1 Rank
			//USER Read: ODT = 0
			//USER Write: ODT = 1
			odt_mask_0 = 0x0;
			odt_mask_1 = 0x1;
		} else if(RW_MGR_MEM_NUMBER_OF_RANKS == 2) { 
			//USER 2 Ranks
			if(RW_MGR_MEM_NUMBER_OF_CS_PER_DIMM == 1 ||
			   (RDIMM && RW_MGR_MEM_NUMBER_OF_CS_PER_DIMM == 2 
			   && RW_MGR_MEM_CHIP_SELECT_WIDTH == 4)) {
				//USER - Dual-Slot , Single-Rank (1 chip-select per DIMM)
				//USER OR
				//USER - RDIMM, 4 total CS (2 CS per DIMM) means 2 DIMM
				//USER Since MEM_NUMBER_OF_RANKS is 2 they are both single rank
				//USER with 2 CS each (special for RDIMM)
				//USER Read: Turn on ODT on the opposite rank
				//USER Write: Turn on ODT on all ranks
				odt_mask_0 = 0x3 & ~(1 << rank);
				odt_mask_1 = 0x3;
			} else {
				//USER - Single-Slot , Dual-rank DIMMs (2 chip-selects per DIMM)
				//USER Read: Turn on ODT off on all ranks
				//USER Write: Turn on ODT on active rank
				odt_mask_0 = 0x0;
				odt_mask_1 = 0x3 & (1 << rank);
			}
				} else {
			//USER 4 Ranks
			//USER Read:
			//USER ----------+-----------------------+
			//USER           |                       |
			//USER           |         ODT           |
			//USER Read From +-----------------------+
			//USER   Rank    |  3  |  2  |  1  |  0  |
			//USER ----------+-----+-----+-----+-----+
			//USER     0     |  0  |  1  |  0  |  0  |
			//USER     1     |  1  |  0  |  0  |  0  |
			//USER     2     |  0  |  0  |  0  |  1  |
			//USER     3     |  0  |  0  |  1  |  0  |
			//USER ----------+-----+-----+-----+-----+
			//USER
			//USER Write:
			//USER ----------+-----------------------+
			//USER           |                       |
			//USER           |         ODT           |
			//USER Write To  +-----------------------+
			//USER   Rank    |  3  |  2  |  1  |  0  |
			//USER ----------+-----+-----+-----+-----+
			//USER     0     |  0  |  1  |  0  |  1  |
			//USER     1     |  1  |  0  |  1  |  0  |
			//USER     2     |  0  |  1  |  0  |  1  |
			//USER     3     |  1  |  0  |  1  |  0  |
			//USER ----------+-----+-----+-----+-----+
			switch(rank)
			{
				case 0:
					odt_mask_0 = 0x4;
					odt_mask_1 = 0x5;
				break;
				case 1:
					odt_mask_0 = 0x8;
					odt_mask_1 = 0xA;
				break;
				case 2:
					odt_mask_0 = 0x1;
					odt_mask_1 = 0x5;
				break;
				case 3:
					odt_mask_0 = 0x2;
					odt_mask_1 = 0xA;
				break;
			}
		}
	}
	else
	{
		odt_mask_0 = 0x0;
		odt_mask_1 = 0x0;
	}

#if MRS_MIRROR_PING_PONG_ATSO
	// See set_cs_and_odt_mask_for_ping_pong_atso
	cs_and_odt_mask = 
			(0xFC) |
			((0xFF & odt_mask_0) << 8) |
			((0xFF & odt_mask_1) << 16);
#else
	if(RDIMM && RW_MGR_MEM_NUMBER_OF_CS_PER_DIMM == 2 
	   && RW_MGR_MEM_CHIP_SELECT_WIDTH == 4 && RW_MGR_MEM_NUMBER_OF_RANKS == 2) {
		//USER See RDIMM special case above
		cs_and_odt_mask = 
			(0xFF & ~(1 << (2*rank))) |
			((0xFF & odt_mask_0) << 8) |
			((0xFF & odt_mask_1) << 16);
	} else if (LRDIMM) {
#if LRDIMM
		// USER LRDIMM special cases - When RM=2, CS[2] is remapped to A[16] so skip it,
		// USER and when RM=4, CS[3:2] are remapped to A[17:16] so skip them both.
		alt_u32 lrdimm_rank = 0;
		alt_u32 lrdimm_rank_mask = 0;

		//USER When rank multiplication is active, the remapped CS pins must be forced low
		//USER instead of high for proper targetted RTT_NOM programming.
		if (LRDIMM_RANK_MULTIPLICATION_FACTOR == 2) {
			// USER Mask = CS[5:0] = 011011
			lrdimm_rank_mask = (0x3 | (0x3 << 3));
		} else if (LRDIMM_RANK_MULTIPLICATION_FACTOR == 4) {
			// USER Mask = CS[7:0] = 00110011
			lrdimm_rank_mask = (0x3 | (0x3 << 4));
		}

		// USER Handle LRDIMM cases where Rank multiplication may be active
		if (((RW_MGR_MEM_CHIP_SELECT_WIDTH/RW_MGR_MEM_NUMBER_OF_CS_PER_DIMM) == 1)) {
			// USER Single-DIMM case
			lrdimm_rank = ~(1 << rank);
		} else if ((RW_MGR_MEM_CHIP_SELECT_WIDTH/RW_MGR_MEM_NUMBER_OF_CS_PER_DIMM) == 2) {
			if (rank < (RW_MGR_MEM_NUMBER_OF_RANKS >> 1)) {
			// USER Dual-DIMM case, accessing first slot
				lrdimm_rank = ~(1 << rank);
			} else {
			// USER Dual-DIMM case, accessing second slot
				lrdimm_rank = ~(1 << (rank + RW_MGR_MEM_NUMBER_OF_CS_PER_DIMM - (RW_MGR_MEM_NUMBER_OF_RANKS>>1)));
			}
		}
		cs_and_odt_mask = 
			(lrdimm_rank_mask & lrdimm_rank) |
			((0xFF & odt_mask_0) << 8) |
			((0xFF & odt_mask_1) << 16);
#endif // LRDIMM
	} else {
		cs_and_odt_mask = 
			(0xFF & ~(1 << rank)) |
			((0xFF & odt_mask_0) << 8) |
			((0xFF & odt_mask_1) << 16);
	}
#endif

	IOWR_32DIRECT (RW_MGR_SET_CS_AND_ODT_MASK, 0, cs_and_odt_mask);
}
#else
#if DDR2
void set_rank_and_odt_mask(alt_u32 rank, alt_u32 odt_mode)
{
	alt_u32 odt_mask_0 = 0;
	alt_u32 odt_mask_1 = 0;
	alt_u32 cs_and_odt_mask;

	if(odt_mode == RW_MGR_ODT_MODE_READ_WRITE)
	{
		if(RW_MGR_MEM_NUMBER_OF_RANKS == 1) { 
			//USER 1 Rank
			//USER Read: ODT = 0
			//USER Write: ODT = 1
			odt_mask_0 = 0x0;
			odt_mask_1 = 0x1;
		} else if(RW_MGR_MEM_NUMBER_OF_RANKS == 2) { 
			//USER 2 Ranks
			if(RW_MGR_MEM_NUMBER_OF_CS_PER_DIMM == 1 ||
			   (RDIMM && RW_MGR_MEM_NUMBER_OF_CS_PER_DIMM == 2 
			   && RW_MGR_MEM_CHIP_SELECT_WIDTH == 4)) {
				//USER - Dual-Slot , Single-Rank (1 chip-select per DIMM)
				//USER OR
				//USER - RDIMM, 4 total CS (2 CS per DIMM) means 2 DIMM
				//USER Since MEM_NUMBER_OF_RANKS is 2 they are both single rank
				//USER with 2 CS each (special for RDIMM)
				//USER Read/Write: Turn on ODT on the opposite rank
				odt_mask_0 = 0x3 & ~(1 << rank);
				odt_mask_1 = 0x3 & ~(1 << rank);
			} else {
				//USER - Single-Slot , Dual-rank DIMMs (2 chip-selects per DIMM)
				//USER Read: Turn on ODT off on all ranks
				//USER Write: Turn on ODT on active rank
				odt_mask_0 = 0x0;
				odt_mask_1 = 0x3 & (1 << rank);
			}
		} else { 
			//USER 4 Ranks
			//USER Read/Write:
			//USER -----------+-----------------------+
			//USER            |                       |
			//USER            |         ODT           |
			//USER Read/Write |                       |
			//USER   From     +-----------------------+
			//USER   Rank     |  3  |  2  |  1  |  0  |
			//USER -----------+-----+-----+-----+-----+
			//USER     0      |  0  |  1  |  0  |  0  |
			//USER     1      |  1  |  0  |  0  |  0  |
			//USER     2      |  0  |  0  |  0  |  1  |
			//USER     3      |  0  |  0  |  1  |  0  |
			//USER -----------+-----+-----+-----+-----+
			switch(rank)
			{
				case 0:
					odt_mask_0 = 0x4;
					odt_mask_1 = 0x4;
				break;
				case 1:
					odt_mask_0 = 0x8;
					odt_mask_1 = 0x8;
				break;
				case 2:
					odt_mask_0 = 0x1;
					odt_mask_1 = 0x1;
				break;
				case 3:
					odt_mask_0 = 0x2;
					odt_mask_1 = 0x2;
				break;
			}
		}
	}
	else
	{
		odt_mask_0 = 0x0;
		odt_mask_1 = 0x0;
	}

	if(RDIMM && RW_MGR_MEM_NUMBER_OF_CS_PER_DIMM == 2 
	   && RW_MGR_MEM_CHIP_SELECT_WIDTH == 4 && RW_MGR_MEM_NUMBER_OF_RANKS == 2) {
		//USER See RDIMM/LRDIMM special case above
		cs_and_odt_mask = 
			(0xFF & ~(1 << (2*rank))) |
			((0xFF & odt_mask_0) << 8) |
			((0xFF & odt_mask_1) << 16);
	} else {
		cs_and_odt_mask = 
			(0xFF & ~(1 << rank)) |
			((0xFF & odt_mask_0) << 8) |
			((0xFF & odt_mask_1) << 16);
	}

	IOWR_32DIRECT (RW_MGR_SET_CS_AND_ODT_MASK, 0, cs_and_odt_mask);
}
#else // QDRII and RLDRAMx
void set_rank_and_odt_mask(alt_u32 rank, alt_u32 odt_mode)
{
	alt_u32 cs_and_odt_mask = 
		(0xFF & ~(1 << rank));

	IOWR_32DIRECT (RW_MGR_SET_CS_AND_ODT_MASK, 0, cs_and_odt_mask);
}
#endif
#endif

//USER Given a rank, select the set of shadow registers that is responsible for the
//USER delays of such rank, so that subsequent SCC updates will go to those shadow
//USER registers. 
void select_shadow_regs_for_update (alt_u32 rank, alt_u32 group, alt_u32 update_scan_chains)
{
#if USE_SHADOW_REGS
	alt_u32 rank_one_hot = (0xFF & (1 << rank));
	
	//USER Assert afi_rrank and afi_wrank. These signals ultimately drive
	//USER the read/write rank select signals which select the shadow register.
	IOWR_32DIRECT (RW_MGR_SET_ACTIVE_RANK, 0, rank_one_hot);
	
	//USER Cause the SCC manager to switch its register file, which is used as
	//USER local cache of the various dtap/ptap settings. There's one register file
	//USER per shadow register set.
	IOWR_32DIRECT (SCC_MGR_ACTIVE_RANK, 0, rank_one_hot);
		
	if (update_scan_chains) {
		alt_u32 i;
	
		//USER On the read side, a memory read is required because the read rank
		//USER select signal (as well as the postamble delay chain settings) is clocked
		//USER into the periphery by the postamble signal. Simply asserting afi_rrank
		//USER is not enough. If update_scc_regfile is not set, we assume there'll be a 
		//USER subsequent read that'll handle this.
		for (i = 0; i < RW_MGR_MEM_NUMBER_OF_RANKS; ++i) {
			
			//USER The dummy read can go to any non-skipped rank.
			//USER Skipped ranks are uninitialized and their banks are un-activated.
			//USER Accessing skipped ranks can lead to bad behavior.
			if (! param->skip_ranks[i]) {
			
				set_rank_and_odt_mask(i, RW_MGR_ODT_MODE_READ_WRITE);
				
				// must re-assert afi_wrank/afi_rrank prior to issuing read 
				// because set_rank_and_odt_mask may have changed the signals.
				IOWR_32DIRECT (RW_MGR_SET_ACTIVE_RANK, 0, rank_one_hot);
				
				IOWR_32DIRECT (RW_MGR_LOAD_CNTR_1, 0, 0x10);
				IOWR_32DIRECT (RW_MGR_LOAD_JUMP_ADD_1, 0, __RW_MGR_READ_B2B_WAIT1);

				IOWR_32DIRECT (RW_MGR_LOAD_CNTR_2, 0, 0x10);
				IOWR_32DIRECT (RW_MGR_LOAD_JUMP_ADD_2, 0, __RW_MGR_READ_B2B_WAIT2);
				
				IOWR_32DIRECT (RW_MGR_LOAD_CNTR_0, 0, 0x0);
				IOWR_32DIRECT (RW_MGR_LOAD_JUMP_ADD_0, 0, __RW_MGR_READ_B2B);
			
				IOWR_32DIRECT (RW_MGR_LOAD_CNTR_3, 0, 0x0);
				IOWR_32DIRECT (RW_MGR_LOAD_JUMP_ADD_3, 0, __RW_MGR_READ_B2B);
			
				IOWR_32DIRECT (RW_MGR_RUN_ALL_GROUPS, 0, __RW_MGR_READ_B2B);
				
				//USER The dummy read above may cause the DQS enable signal to be stuck high.
				//USER The following corrects this.
				IOWR_32DIRECT (RW_MGR_RUN_ALL_GROUPS, 0, __RW_MGR_CLEAR_DQS_ENABLE);				
				
				set_rank_and_odt_mask(i, RW_MGR_ODT_MODE_OFF);
				
				break;
			}
		}
		
		//USER Reset the fifos to get pointers to known state 
		IOWR_32DIRECT (PHY_MGR_CMD_FIFO_RESET, 0, 0);
		IOWR_32DIRECT (RW_MGR_RESET_READ_DATAPATH, 0, 0);	
	
		//USER On the write side the afi_wrank signal eventually propagates to the I/O 
		//USER through the write datapath. We need to make sure we wait long enough for
		//USER this to happen. The operations above should be enough, hence no extra delay
		//USER inserted here.
	
		//USER Make sure the data in the I/O scan chains are in-sync with the register
		//USER file inside the SCC manager. If we don't do this, a subsequent SCC_UPDATE
		//USER may cause stale data for the other shadow register to be loaded. This must
		//USER be done for every scan chain of the current group. Note that in shadow
		//USER register mode, the SCC_UPDATE signal is per-group.
		IOWR_32DIRECT (SCC_MGR_GROUP_COUNTER, 0, group);
		
		IOWR_32DIRECT (SCC_MGR_DQS_ENA, 0, group);
		IOWR_32DIRECT (SCC_MGR_DQS_IO_ENA, 0, 0);
		
		for (i = 0; i < RW_MGR_MEM_DQ_PER_WRITE_DQS; i++) {
			IOWR_32DIRECT (SCC_MGR_DQ_ENA, 0, i);
		}
		for (i = 0; i < RW_MGR_NUM_DM_PER_WRITE_GROUP; i++) {
			IOWR_32DIRECT (SCC_MGR_DM_ENA, 0, i);
		}
	}

	//USER Map the rank to its shadow reg
	select_curr_shadow_reg_using_rank(rank);
#endif
}

#if HHP_HPS
void scc_mgr_initialize(void)
{
	// Clear register file for HPS
	// 16 (2^4) is the size of the full register file in the scc mgr:
	//	RFILE_DEPTH = log2(MEM_DQ_PER_DQS + 1 + MEM_DM_PER_DQS + MEM_IF_READ_DQS_WIDTH - 1) + 1;
	alt_u32 i;
	for (i = 0; i < 16; i++) {
		DPRINT(1, "Clearing SCC RFILE index %lu", i);
		IOWR_32DIRECT(SCC_MGR_HHP_RFILE, i << 2, 0);
	}
}
#endif

inline void scc_mgr_set_dqs_bus_in_delay(alt_u32 read_group, alt_u32 delay)
{
	ALTERA_ASSERT(read_group < RW_MGR_MEM_IF_READ_DQS_WIDTH);

	// Load the setting in the SCC manager
	WRITE_SCC_DQS_IN_DELAY(read_group, delay);

	// Make the setting in the TCL report
	TCLRPT_SET(debug_cal_report->cal_dqs_in_settings[curr_shadow_reg][read_group].dqs_bus_in_delay, delay);

}

static inline void scc_mgr_set_dqs_io_in_delay(alt_u32 write_group, alt_u32 delay)
{
	ALTERA_ASSERT(write_group < RW_MGR_MEM_IF_WRITE_DQS_WIDTH);

	// Load the setting in the SCC manager
	WRITE_SCC_DQS_IO_IN_DELAY(delay);

	// Make the setting in the TCL report
	TCLRPT_SET(debug_cal_report->cal_dqs_out_settings[curr_shadow_reg][write_group].dqs_io_in_delay, delay);

}

static inline void scc_mgr_set_dqs_en_phase(alt_u32 read_group, alt_u32 phase)
{
	ALTERA_ASSERT(read_group < RW_MGR_MEM_IF_READ_DQS_WIDTH);

	// Load the setting in the SCC manager
	WRITE_SCC_DQS_EN_PHASE(read_group, phase);

	// Make the setting in the TCL report
	TCLRPT_SET(debug_cal_report->cal_dqs_in_settings[curr_shadow_reg][read_group].dqs_en_phase, phase);

}

void scc_mgr_set_dqs_en_phase_all_ranks (alt_u32 read_group, alt_u32 phase)
{
	alt_u32 r;
	alt_u32 update_scan_chains;
		
	for (r = 0; r < RW_MGR_MEM_NUMBER_OF_RANKS; r += NUM_RANKS_PER_SHADOW_REG) {
		//USER although the h/w doesn't support different phases per shadow register,
		//USER for simplicity our scc manager modeling keeps different phase settings per 
		//USER shadow reg, and it's important for us to keep them in sync to match h/w.
		//USER for efficiency, the scan chain update should occur only once to sr0.
		update_scan_chains = (r == 0) ? 1 : 0;
		
		select_shadow_regs_for_update(r, read_group, update_scan_chains);
		scc_mgr_set_dqs_en_phase(read_group, phase);
		
		if (update_scan_chains) {
			IOWR_32DIRECT (SCC_MGR_DQS_ENA, 0, read_group);
			IOWR_32DIRECT (SCC_MGR_UPD, 0, 0);
		}
	}
}


static inline void scc_mgr_set_dqdqs_output_phase(alt_u32 write_group, alt_u32 phase)
{
	ALTERA_ASSERT(write_group < RW_MGR_MEM_IF_WRITE_DQS_WIDTH);

	#if CALIBRATE_BIT_SLIPS
	alt_u32 num_fr_slips = 0;
	while (phase > IO_DQDQS_OUT_PHASE_MAX) {
		phase -= IO_DLL_CHAIN_LENGTH;
		num_fr_slips++;
	}
	IOWR_32DIRECT (PHY_MGR_FR_SHIFT, write_group*4, num_fr_slips);
#endif
	
	// Load the setting in the SCC manager
	WRITE_SCC_DQDQS_OUT_PHASE(write_group, phase);

	// Make the setting in the TCL report
	TCLRPT_SET(debug_cal_report->cal_dqs_out_settings[curr_shadow_reg][write_group].dqdqs_out_phase, phase);

}

void scc_mgr_set_dqdqs_output_phase_all_ranks (alt_u32 write_group, alt_u32 phase)
{
	alt_u32 r;
	alt_u32 update_scan_chains;
		
	for (r = 0; r < RW_MGR_MEM_NUMBER_OF_RANKS; r += NUM_RANKS_PER_SHADOW_REG) {
		//USER although the h/w doesn't support different phases per shadow register,
		//USER for simplicity our scc manager modeling keeps different phase settings per 
		//USER shadow reg, and it's important for us to keep them in sync to match h/w.
		//USER for efficiency, the scan chain update should occur only once to sr0.
		update_scan_chains = (r == 0) ? 1 : 0;
		
		select_shadow_regs_for_update(r, write_group, update_scan_chains);
		scc_mgr_set_dqdqs_output_phase(write_group, phase);
		
		if (update_scan_chains) {
			IOWR_32DIRECT (SCC_MGR_DQS_ENA, 0, write_group);
			IOWR_32DIRECT (SCC_MGR_UPD, 0, 0);
		}
	}
}


static inline void scc_mgr_set_dqs_en_delay(alt_u32 read_group, alt_u32 delay)
{
	ALTERA_ASSERT(read_group < RW_MGR_MEM_IF_READ_DQS_WIDTH);

	// Load the setting in the SCC manager
	WRITE_SCC_DQS_EN_DELAY(read_group, delay);

	// Make the setting in the TCL report
	TCLRPT_SET(debug_cal_report->cal_dqs_in_settings[curr_shadow_reg][read_group].dqs_en_delay, delay);

}

void scc_mgr_set_dqs_en_delay_all_ranks (alt_u32 read_group, alt_u32 delay)
{
	alt_u32 r;
		
	for (r = 0; r < RW_MGR_MEM_NUMBER_OF_RANKS; r += NUM_RANKS_PER_SHADOW_REG) {
	
		select_shadow_regs_for_update(r, read_group, 0);
		
		scc_mgr_set_dqs_en_delay(read_group, delay);

		IOWR_32DIRECT (SCC_MGR_DQS_ENA, 0, read_group);
		
#if !USE_SHADOW_REGS		
		// In shadow register mode, the T11 settings are stored in registers
		// in the core, which are updated by the DQS_ENA signals. Not issuing
		// the SCC_MGR_UPD command allows us to save lots of rank switching
		// overhead, by calling select_shadow_regs_for_update with update_scan_chains
		// set to 0.
		IOWR_32DIRECT (SCC_MGR_UPD, 0, 0);
#endif		
	}	
}

static void scc_mgr_set_oct_out1_delay(alt_u32 write_group, alt_u32 delay)
{
	alt_u32 read_group;

	ALTERA_ASSERT(write_group < RW_MGR_MEM_IF_WRITE_DQS_WIDTH);

	// Load the setting in the SCC manager
	// Although OCT affects only write data, the OCT delay is controlled by the DQS logic block
	// which is instantiated once per read group. For protocols where a write group consists
	// of multiple read groups, the setting must be set multiple times.
	for (read_group = write_group * RW_MGR_MEM_IF_READ_DQS_WIDTH / RW_MGR_MEM_IF_WRITE_DQS_WIDTH;
		 read_group < (write_group + 1) * RW_MGR_MEM_IF_READ_DQS_WIDTH / RW_MGR_MEM_IF_WRITE_DQS_WIDTH;
		 ++read_group) {
		 
		WRITE_SCC_OCT_OUT1_DELAY(read_group, delay);
	}

	// Make the setting in the TCL report
	TCLRPT_SET(debug_cal_report->cal_dqs_out_settings[curr_shadow_reg][write_group].oct_out_delay1, delay);

}

static void scc_mgr_set_oct_out2_delay(alt_u32 write_group, alt_u32 delay)
{
	alt_u32 read_group;

	ALTERA_ASSERT(write_group < RW_MGR_MEM_IF_WRITE_DQS_WIDTH);

	// Load the setting in the SCC manager
	// Although OCT affects only write data, the OCT delay is controlled by the DQS logic block
	// which is instantiated once per read group. For protocols where a write group consists
	// of multiple read groups, the setting must be set multiple times.
	for (read_group = write_group * RW_MGR_MEM_IF_READ_DQS_WIDTH / RW_MGR_MEM_IF_WRITE_DQS_WIDTH;
		 read_group < (write_group + 1) * RW_MGR_MEM_IF_READ_DQS_WIDTH / RW_MGR_MEM_IF_WRITE_DQS_WIDTH;
		 ++read_group) {
	
		WRITE_SCC_OCT_OUT2_DELAY(read_group, delay);
	}

	// Make the setting in the TCL report
	TCLRPT_SET(debug_cal_report->cal_dqs_out_settings[curr_shadow_reg][write_group].oct_out_delay2, delay);

}

static inline void scc_mgr_set_dqs_bypass(alt_u32 write_group, alt_u32 bypass)
{
	// Load the setting in the SCC manager
	WRITE_SCC_DQS_BYPASS(write_group, bypass);
}

inline void scc_mgr_set_dq_out1_delay(alt_u32 write_group, alt_u32 dq_in_group, alt_u32 delay)
{
#if ENABLE_TCL_DEBUG || ENABLE_ASSERT
	alt_u32 dq = write_group*RW_MGR_MEM_DQ_PER_WRITE_DQS + dq_in_group;
#endif

	ALTERA_ASSERT(write_group < RW_MGR_MEM_IF_WRITE_DQS_WIDTH);
	ALTERA_ASSERT(dq < RW_MGR_MEM_DATA_WIDTH);

	// Load the setting in the SCC manager
	WRITE_SCC_DQ_OUT1_DELAY(dq_in_group, delay);

	// Make the setting in the TCL report
	TCLRPT_SET(debug_cal_report->cal_dq_settings[curr_shadow_reg][dq].dq_out_delay1, delay);

}

inline void scc_mgr_set_dq_out2_delay(alt_u32 write_group, alt_u32 dq_in_group, alt_u32 delay)
{
#if ENABLE_TCL_DEBUG || ENABLE_ASSERT
	alt_u32 dq = write_group*RW_MGR_MEM_DQ_PER_WRITE_DQS + dq_in_group;
#endif

	ALTERA_ASSERT(write_group < RW_MGR_MEM_IF_WRITE_DQS_WIDTH);
	ALTERA_ASSERT(dq < RW_MGR_MEM_DATA_WIDTH);

	// Load the setting in the SCC manager
	WRITE_SCC_DQ_OUT2_DELAY(dq_in_group, delay);

	// Make the setting in the TCL report
	TCLRPT_SET(debug_cal_report->cal_dq_settings[curr_shadow_reg][dq].dq_out_delay2, delay);

}

inline void scc_mgr_set_dq_in_delay(alt_u32 write_group, alt_u32 dq_in_group, alt_u32 delay)
{
#if ENABLE_TCL_DEBUG || ENABLE_ASSERT
	alt_u32 dq = write_group*RW_MGR_MEM_DQ_PER_WRITE_DQS + dq_in_group;
#endif

	ALTERA_ASSERT(write_group < RW_MGR_MEM_IF_WRITE_DQS_WIDTH);
	ALTERA_ASSERT(dq < RW_MGR_MEM_DATA_WIDTH);

	// Load the setting in the SCC manager
	WRITE_SCC_DQ_IN_DELAY(dq_in_group, delay);

	// Make the setting in the TCL report
	TCLRPT_SET(debug_cal_report->cal_dq_settings[curr_shadow_reg][dq].dq_in_delay, delay);

}

static inline void scc_mgr_set_dq_bypass(alt_u32 write_group, alt_u32 dq_in_group, alt_u32 bypass)
{
	// Load the setting in the SCC manager
	WRITE_SCC_DQ_BYPASS(dq_in_group, bypass);
}

static inline void scc_mgr_set_rfifo_mode(alt_u32 write_group, alt_u32 dq_in_group, alt_u32 mode)
{
	// Load the setting in the SCC manager
	WRITE_SCC_RFIFO_MODE(dq_in_group, mode);
}

static inline void scc_mgr_set_hhp_extras(void)
{
	// Load the fixed setting in the SCC manager
	// bits: 0:0 = 1'b1   - dqs bypass
	// bits: 1:1 = 1'b1   - dq bypass
	// bits: 4:2 = 3'b001   - rfifo_mode
	// bits: 6:5 = 2'b01  - rfifo clock_select
	// bits: 7:7 = 1'b0  - separate gating from ungating setting
	// bits: 8:8 = 1'b0  - separate OE from Output delay setting
	alt_u32 value = (0<<8) | (0<<7) | (1<<5) | (1<<2) | (1<<1) | (1<<0);
	WRITE_SCC_HHP_EXTRAS(value);
}

static inline void scc_mgr_set_hhp_dqse_map(void)
{
	// Load the fixed setting in the SCC manager
	WRITE_SCC_HHP_DQSE_MAP(0);
}

static inline void scc_mgr_set_dqs_out1_delay(alt_u32 write_group, alt_u32 delay)
{
	ALTERA_ASSERT(write_group < RW_MGR_MEM_IF_WRITE_DQS_WIDTH);

	// Load the setting in the SCC manager
	WRITE_SCC_DQS_IO_OUT1_DELAY(delay);

	// Make the setting in the TCL report
	TCLRPT_SET(debug_cal_report->cal_dqs_out_settings[curr_shadow_reg][write_group].dqs_out_delay1, delay);

}

static inline void scc_mgr_set_dqs_out2_delay(alt_u32 write_group, alt_u32 delay)
{
	ALTERA_ASSERT(write_group < RW_MGR_MEM_IF_WRITE_DQS_WIDTH);

	// Load the setting in the SCC manager
	WRITE_SCC_DQS_IO_OUT2_DELAY(delay);

	// Make the setting in the TCL report
	TCLRPT_SET(debug_cal_report->cal_dqs_out_settings[curr_shadow_reg][write_group].dqs_out_delay2, delay);

}

inline void scc_mgr_set_dm_out1_delay(alt_u32 write_group, alt_u32 dm, alt_u32 delay)
{
	ALTERA_ASSERT(write_group < RW_MGR_MEM_IF_WRITE_DQS_WIDTH);
	ALTERA_ASSERT(dm < RW_MGR_NUM_DM_PER_WRITE_GROUP);

	// Load the setting in the SCC manager
	WRITE_SCC_DM_IO_OUT1_DELAY(dm, delay);

	// Make the setting in the TCL report

	if (RW_MGR_NUM_TRUE_DM_PER_WRITE_GROUP > 0)
	{
		TCLRPT_SET(debug_cal_report->cal_dm_settings[curr_shadow_reg][write_group][dm].dm_out_delay1, delay);
	}
}

inline void scc_mgr_set_dm_out2_delay(alt_u32 write_group, alt_u32 dm, alt_u32 delay)
{
	ALTERA_ASSERT(write_group < RW_MGR_MEM_IF_WRITE_DQS_WIDTH);
	ALTERA_ASSERT(dm < RW_MGR_NUM_DM_PER_WRITE_GROUP);

	// Load the setting in the SCC manager
	WRITE_SCC_DM_IO_OUT2_DELAY(dm, delay);

	// Make the setting in the TCL report

	if (RW_MGR_NUM_TRUE_DM_PER_WRITE_GROUP > 0)
	{
		TCLRPT_SET(debug_cal_report->cal_dm_settings[curr_shadow_reg][write_group][dm].dm_out_delay2, delay);
	}
}

static inline void scc_mgr_set_dm_in_delay(alt_u32 write_group, alt_u32 dm, alt_u32 delay)
{
	ALTERA_ASSERT(write_group < RW_MGR_MEM_IF_WRITE_DQS_WIDTH);
	ALTERA_ASSERT(dm < RW_MGR_NUM_DM_PER_WRITE_GROUP);

	// Load the setting in the SCC manager
	WRITE_SCC_DM_IO_IN_DELAY(dm, delay);

	// Make the setting in the TCL report

	if (RW_MGR_NUM_TRUE_DM_PER_WRITE_GROUP > 0)
	{
		TCLRPT_SET(debug_cal_report->cal_dm_settings[curr_shadow_reg][write_group][dm].dm_in_delay, delay);
	}
}

static inline void scc_mgr_set_dm_bypass(alt_u32 write_group, alt_u32 dm, alt_u32 bypass)
{
	// Load the setting in the SCC manager
	WRITE_SCC_DM_BYPASS(dm, bypass);
}

//USER Zero all DQS config
// TODO: maybe rename to scc_mgr_zero_dqs_config (or something)
void scc_mgr_zero_all (void)
{
	alt_u32 i, r;
		
	//USER Zero all DQS config settings, across all groups and all shadow registers
	for (r = 0; r < RW_MGR_MEM_NUMBER_OF_RANKS; r += NUM_RANKS_PER_SHADOW_REG) {
	
		// Strictly speaking this should be called once per group to make
		// sure each group's delay chain is refreshed from the SCC register file,
		// but since we're resetting all delay chains anyway, we can save some
		// runtime by calling select_shadow_regs_for_update just once to switch
		// rank.
		select_shadow_regs_for_update(r, 0, 1);

		for (i = 0; i < RW_MGR_MEM_IF_READ_DQS_WIDTH; i++) {
			// The phases actually don't exist on a per-rank basis, but there's
			// no harm updating them several times, so let's keep the code simple.
			scc_mgr_set_dqs_bus_in_delay(i, IO_DQS_IN_RESERVE);
			scc_mgr_set_dqs_en_phase(i, 0);
			scc_mgr_set_dqs_en_delay(i, 0);
		}

		for (i = 0; i < RW_MGR_MEM_IF_WRITE_DQS_WIDTH; i++) {
			scc_mgr_set_dqdqs_output_phase(i, 0);
#if ARRIAV || CYCLONEV
			// av/cv don't have out2
			scc_mgr_set_oct_out1_delay(i, IO_DQS_OUT_RESERVE);
#else
			scc_mgr_set_oct_out1_delay(i, 0);
			scc_mgr_set_oct_out2_delay(i, IO_DQS_OUT_RESERVE);
#endif
		}

		//USER multicast to all DQS group enables
		IOWR_32DIRECT (SCC_MGR_DQS_ENA, 0, 0xff);
		
#if USE_SHADOW_REGS		
		//USER in shadow-register mode, SCC_UPDATE is done on a per-group basis
		//USER unless we explicitly ask for a multicast via the group counter
		IOWR_32DIRECT (SCC_MGR_GROUP_COUNTER, 0, 0xFF);
#endif		
		IOWR_32DIRECT (SCC_MGR_UPD, 0, 0);
	}
}

void scc_set_bypass_mode(alt_u32 write_group, alt_u32 mode)
{
	// mode = 0 : Do NOT bypass - Half Rate Mode
	// mode = 1 : Bypass - Full Rate Mode

#if !HHP_HPS
	alt_u32 i;
#endif

#if HHP_HPS
	// only need to set once for all groups, pins, dq, dqs, dm
	if (write_group == 0) {
		DPRINT(1, "Setting HHP Extras");
		scc_mgr_set_hhp_extras();
		DPRINT(1, "Done Setting HHP Extras");
	}
#endif
	
#if !HHP_HPS
	for (i = 0; i < RW_MGR_MEM_DQ_PER_WRITE_DQS; i++)
	{
		scc_mgr_set_dq_bypass(write_group, i, mode);
		scc_mgr_set_rfifo_mode(write_group, i, mode);
	}
#endif

	//USER multicast to all DQ enables 
	IOWR_32DIRECT (SCC_MGR_DQ_ENA, 0, 0xff);

#if !HHP_HPS
	for (i = 0; i < RW_MGR_NUM_DM_PER_WRITE_GROUP; i++)
	{
		scc_mgr_set_dm_bypass(write_group, i, mode);
	}
#endif

	IOWR_32DIRECT (SCC_MGR_DM_ENA, 0, 0xff);

#if !HHP_HPS
	scc_mgr_set_dqs_bypass(write_group, mode);
#endif

	//USER update current DQS IO enable
	IOWR_32DIRECT (SCC_MGR_DQS_IO_ENA, 0, 0);

	//USER update the DQS logic
	IOWR_32DIRECT (SCC_MGR_DQS_ENA, 0, write_group);

	//USER hit update
	IOWR_32DIRECT (SCC_MGR_UPD, 0, 0);
}

// Moving up to avoid warnings
void scc_mgr_load_dqs_for_write_group (alt_u32 write_group)
{
	alt_u32 read_group;
	
	// Although OCT affects only write data, the OCT delay is controlled by the DQS logic block
	// which is instantiated once per read group. For protocols where a write group consists
	// of multiple read groups, the setting must be scanned multiple times.
	for (read_group = write_group * RW_MGR_MEM_IF_READ_DQS_WIDTH / RW_MGR_MEM_IF_WRITE_DQS_WIDTH;
		 read_group < (write_group + 1) * RW_MGR_MEM_IF_READ_DQS_WIDTH / RW_MGR_MEM_IF_WRITE_DQS_WIDTH;
		 ++read_group) {
		 
		IOWR_32DIRECT (SCC_MGR_DQS_ENA, 0, read_group);
	}
}

void scc_mgr_zero_group (alt_u32 write_group, alt_u32 test_begin, alt_32 out_only)
{
	alt_u32 i, r;

	for (r = 0; r < RW_MGR_MEM_NUMBER_OF_RANKS; r += NUM_RANKS_PER_SHADOW_REG) {	
		
		select_shadow_regs_for_update(r, write_group, 1);

		//USER Zero all DQ config settings
		for (i = 0; i < RW_MGR_MEM_DQ_PER_WRITE_DQS; i++)
		{
			scc_mgr_set_dq_out1_delay(write_group, i, 0);
			scc_mgr_set_dq_out2_delay(write_group, i, IO_DQ_OUT_RESERVE);
			if (!out_only) {
				scc_mgr_set_dq_in_delay(write_group, i, 0);
			}
		}

		//USER multicast to all DQ enables
		IOWR_32DIRECT (SCC_MGR_DQ_ENA, 0, 0xff);

		//USER Zero all DM config settings 
		for (i = 0; i < RW_MGR_NUM_DM_PER_WRITE_GROUP; i++)
		{
			if (!out_only) {
				// Do we really need this?
				scc_mgr_set_dm_in_delay(write_group, i, 0);
			}
			scc_mgr_set_dm_out1_delay(write_group, i, 0);
			scc_mgr_set_dm_out2_delay(write_group, i, IO_DM_OUT_RESERVE);
		}

		//USER multicast to all DM enables
		IOWR_32DIRECT (SCC_MGR_DM_ENA, 0, 0xff);

		//USER zero all DQS io settings 
		if (!out_only) {
			scc_mgr_set_dqs_io_in_delay(write_group, 0);
		}
#if ARRIAV || CYCLONEV
		// av/cv don't have out2
		scc_mgr_set_dqs_out1_delay(write_group, IO_DQS_OUT_RESERVE);
		scc_mgr_set_oct_out1_delay(write_group, IO_DQS_OUT_RESERVE);
		scc_mgr_load_dqs_for_write_group (write_group);
#else
		scc_mgr_set_dqs_out1_delay(write_group, 0);
		scc_mgr_set_dqs_out2_delay(write_group, IO_DQS_OUT_RESERVE);
		scc_mgr_set_oct_out1_delay(write_group, 0);
		scc_mgr_set_oct_out2_delay(write_group, IO_DQS_OUT_RESERVE);
		scc_mgr_load_dqs_for_write_group (write_group);
#endif

		//USER multicast to all DQS IO enables (only 1)
		IOWR_32DIRECT (SCC_MGR_DQS_IO_ENA, 0, 0);

#if USE_SHADOW_REGS		
		//USER in shadow-register mode, SCC_UPDATE is done on a per-group basis
		//USER unless we explicitly ask for a multicast via the group counter
		IOWR_32DIRECT (SCC_MGR_GROUP_COUNTER, 0, 0xFF);
#endif				
		//USER hit update to zero everything 
		IOWR_32DIRECT (SCC_MGR_UPD, 0, 0);
	}
}

//USER load up dqs config settings 

void scc_mgr_load_dqs (alt_u32 dqs)
{
	IOWR_32DIRECT (SCC_MGR_DQS_ENA, 0, dqs);
}


//USER load up dqs io config settings 

void scc_mgr_load_dqs_io (void)
{
	IOWR_32DIRECT (SCC_MGR_DQS_IO_ENA, 0, 0);
}

//USER load up dq config settings 

void scc_mgr_load_dq (alt_u32 dq_in_group)
{
	IOWR_32DIRECT (SCC_MGR_DQ_ENA, 0, dq_in_group);
}

//USER load up dm config settings 

void scc_mgr_load_dm (alt_u32 dm)
{
	IOWR_32DIRECT (SCC_MGR_DM_ENA, 0, dm);
}

//USER apply and load a particular input delay for the DQ pins in a group
//USER group_bgn is the index of the first dq pin (in the write group)

void scc_mgr_apply_group_dq_in_delay (alt_u32 write_group, alt_u32 group_bgn, alt_u32 delay)
{
	alt_u32 i, p;

	for (i = 0, p = group_bgn; i < RW_MGR_MEM_DQ_PER_READ_DQS; i++, p++) {
		scc_mgr_set_dq_in_delay(write_group, p, delay);
		scc_mgr_load_dq (p);
	}
}

//USER apply and load a particular output delay for the DQ pins in a group

void scc_mgr_apply_group_dq_out1_delay (alt_u32 write_group, alt_u32 group_bgn, alt_u32 delay1)
{
	alt_u32 i, p;

	for (i = 0, p = group_bgn; i < RW_MGR_MEM_DQ_PER_WRITE_DQS; i++, p++) {
		scc_mgr_set_dq_out1_delay(write_group, i, delay1);
		scc_mgr_load_dq (i);
	}
}

void scc_mgr_apply_group_dq_out2_delay (alt_u32 write_group, alt_u32 group_bgn, alt_u32 delay2)
{
	alt_u32 i, p;

	for (i = 0, p = group_bgn; i < RW_MGR_MEM_DQ_PER_WRITE_DQS; i++, p++) {
		scc_mgr_set_dq_out2_delay(write_group, i, delay2);
		scc_mgr_load_dq (i);
	}
}

//USER apply and load a particular output delay for the DM pins in a group

void scc_mgr_apply_group_dm_out1_delay (alt_u32 write_group, alt_u32 delay1)
{
	alt_u32 i;

	for (i = 0; i < RW_MGR_NUM_DM_PER_WRITE_GROUP; i++) {
		scc_mgr_set_dm_out1_delay(write_group, i, delay1);
		scc_mgr_load_dm (i);
	}
}


//USER apply and load delay on both DQS and OCT out1
void scc_mgr_apply_group_dqs_io_and_oct_out1 (alt_u32 write_group, alt_u32 delay)
{
	scc_mgr_set_dqs_out1_delay(write_group, delay);
	scc_mgr_load_dqs_io ();

	scc_mgr_set_oct_out1_delay(write_group, delay);
	scc_mgr_load_dqs_for_write_group (write_group);
}

//USER apply and load delay on both DQS and OCT out2
void scc_mgr_apply_group_dqs_io_and_oct_out2 (alt_u32 write_group, alt_u32 delay)
{
	scc_mgr_set_dqs_out2_delay(write_group, delay);
	scc_mgr_load_dqs_io ();

	scc_mgr_set_oct_out2_delay(write_group, delay);
	scc_mgr_load_dqs_for_write_group (write_group);
}

//USER set delay on both DQS and OCT out1 by incrementally changing
//USER the settings one dtap at a time towards the target value, to avoid
//USER breaking the lock of the DLL/PLL on the memory device.
void scc_mgr_set_group_dqs_io_and_oct_out1_gradual (alt_u32 write_group, alt_u32 delay)
{
	alt_u32 d = READ_SCC_DQS_IO_OUT1_DELAY();
	
	while (d > delay) {
		--d;
		scc_mgr_apply_group_dqs_io_and_oct_out1 (write_group, d);
		IOWR_32DIRECT (SCC_MGR_UPD, 0, 0);
		if (QDRII)
		{
			rw_mgr_mem_dll_lock_wait();
		}
	}
	while (d < delay) {
		++d;
		scc_mgr_apply_group_dqs_io_and_oct_out1 (write_group, d);
		IOWR_32DIRECT (SCC_MGR_UPD, 0, 0);
		if (QDRII)
		{
			rw_mgr_mem_dll_lock_wait();
		}
	}	
}

//USER set delay on both DQS and OCT out2 by incrementally changing
//USER the settings one dtap at a time towards the target value, to avoid
//USER breaking the lock of the DLL/PLL on the memory device.
void scc_mgr_set_group_dqs_io_and_oct_out2_gradual (alt_u32 write_group, alt_u32 delay)
{
	alt_u32 d = READ_SCC_DQS_IO_OUT2_DELAY();
	
	while (d > delay) {
		--d;
		scc_mgr_apply_group_dqs_io_and_oct_out2 (write_group, d);
		IOWR_32DIRECT (SCC_MGR_UPD, 0, 0);
		if (QDRII)
		{
			rw_mgr_mem_dll_lock_wait();
		}
	}
	while (d < delay) {
		++d;
		scc_mgr_apply_group_dqs_io_and_oct_out2 (write_group, d);
		IOWR_32DIRECT (SCC_MGR_UPD, 0, 0);
		if (QDRII)
		{
			rw_mgr_mem_dll_lock_wait();
		}
	}	
}

//USER apply a delay to the entire output side: DQ, DM, DQS, OCT 

void scc_mgr_apply_group_all_out_delay (alt_u32 write_group, alt_u32 group_bgn, alt_u32 delay)
{
	//USER dq shift 

	scc_mgr_apply_group_dq_out1_delay (write_group, group_bgn, delay);

	//USER dm shift 

	scc_mgr_apply_group_dm_out1_delay (write_group, delay);

	//USER dqs and oct shift 

	scc_mgr_apply_group_dqs_io_and_oct_out1 (write_group, delay);
}

//USER apply a delay to the entire output side (DQ, DM, DQS, OCT) and to all ranks
void scc_mgr_apply_group_all_out_delay_all_ranks (alt_u32 write_group, alt_u32 group_bgn, alt_u32 delay)
{
	alt_u32 r;
		
	for (r = 0; r < RW_MGR_MEM_NUMBER_OF_RANKS; r += NUM_RANKS_PER_SHADOW_REG) {
	
		select_shadow_regs_for_update(r, write_group, 1);

		scc_mgr_apply_group_all_out_delay (write_group, group_bgn, delay);
		
		IOWR_32DIRECT (SCC_MGR_UPD, 0, 0);
	}
}

//USER apply a delay to the entire output side: DQ, DM, DQS, OCT 

void scc_mgr_apply_group_all_out_delay_add (alt_u32 write_group, alt_u32 group_bgn, alt_u32 delay)
{
	alt_u32 i, p, new_delay;

	//USER dq shift 

	for (i = 0, p = group_bgn; i < RW_MGR_MEM_DQ_PER_WRITE_DQS; i++, p++) {

		new_delay = READ_SCC_DQ_OUT2_DELAY(i);
		new_delay += delay;

		if (new_delay > IO_IO_OUT2_DELAY_MAX) {
			DPRINT(1, "%s(%lu, %lu, %lu) DQ[%lu,%lu]: %lu > %lu => %lu",
			       __func__, write_group, group_bgn, delay, i, p,
			       new_delay, (long unsigned int)IO_IO_OUT2_DELAY_MAX, (long unsigned int)IO_IO_OUT2_DELAY_MAX);
			new_delay = IO_IO_OUT2_DELAY_MAX;
		}

		scc_mgr_set_dq_out2_delay(write_group, i, new_delay);
		scc_mgr_load_dq (i);
	}

	//USER dm shift 

	for (i = 0; i < RW_MGR_NUM_DM_PER_WRITE_GROUP; i++) {
		new_delay = READ_SCC_DM_IO_OUT2_DELAY(i);
		new_delay += delay;

		if (new_delay > IO_IO_OUT2_DELAY_MAX) {
			DPRINT(1, "%s(%lu, %lu, %lu) DM[%lu]: %lu > %lu => %lu",
			       __func__, write_group, group_bgn, delay, i, 
			       new_delay, (long unsigned int)IO_IO_OUT2_DELAY_MAX, (long unsigned int)IO_IO_OUT2_DELAY_MAX);
			new_delay = IO_IO_OUT2_DELAY_MAX;
		}

		scc_mgr_set_dm_out2_delay(write_group, i, new_delay);
		scc_mgr_load_dm (i);
	}

	//USER dqs shift 

	new_delay = READ_SCC_DQS_IO_OUT2_DELAY();
	new_delay += delay;

	if (new_delay > IO_IO_OUT2_DELAY_MAX) {
		DPRINT(1, "%s(%lu, %lu, %lu) DQS: %lu > %d => %d; adding %lu to OUT1",
		       __func__, write_group, group_bgn, delay,
		       new_delay, IO_IO_OUT2_DELAY_MAX, IO_IO_OUT2_DELAY_MAX,
			new_delay - IO_IO_OUT2_DELAY_MAX);
		scc_mgr_set_dqs_out1_delay(write_group, new_delay - IO_IO_OUT2_DELAY_MAX);
		new_delay = IO_IO_OUT2_DELAY_MAX;
	}

	scc_mgr_set_dqs_out2_delay(write_group, new_delay);
	scc_mgr_load_dqs_io ();

	//USER oct shift 

	new_delay = READ_SCC_OCT_OUT2_DELAY(write_group);
	new_delay += delay;

	if (new_delay > IO_IO_OUT2_DELAY_MAX) {
		DPRINT(1, "%s(%lu, %lu, %lu) DQS: %lu > %d => %d; adding %lu to OUT1",
		       __func__, write_group, group_bgn, delay,
		       new_delay, IO_IO_OUT2_DELAY_MAX, IO_IO_OUT2_DELAY_MAX,
			new_delay - IO_IO_OUT2_DELAY_MAX);
		scc_mgr_set_oct_out1_delay(write_group, new_delay - IO_IO_OUT2_DELAY_MAX);
		new_delay = IO_IO_OUT2_DELAY_MAX;
	}

	scc_mgr_set_oct_out2_delay(write_group, new_delay);
	scc_mgr_load_dqs_for_write_group (write_group);
}

//USER apply a delay to the entire output side (DQ, DM, DQS, OCT) and to all ranks
void scc_mgr_apply_group_all_out_delay_add_all_ranks (alt_u32 write_group, alt_u32 group_bgn, alt_u32 delay)
{
	alt_u32 r;
		
	for (r = 0; r < RW_MGR_MEM_NUMBER_OF_RANKS; r += NUM_RANKS_PER_SHADOW_REG) {
	
		select_shadow_regs_for_update(r, write_group, 1);
		
		scc_mgr_apply_group_all_out_delay_add (write_group, group_bgn, delay);

		IOWR_32DIRECT (SCC_MGR_UPD, 0, 0);
	}
}

static inline void scc_mgr_spread_out2_delay_all_ranks (alt_u32 write_group, alt_u32 test_bgn)
{
#if STRATIXV || ARRIAVGZ
	alt_u32 found;
	alt_u32 i;
	alt_u32 p;
	alt_u32 d;
	alt_u32 r;
		
	const alt_u32 delay_step = IO_IO_OUT2_DELAY_MAX/(RW_MGR_MEM_DQ_PER_WRITE_DQS-1); /* we start at zero, so have one less dq to devide among */
	
	TRACE_FUNC("(%lu,%lu)", write_group, test_bgn);

	for (r = 0; r < RW_MGR_MEM_NUMBER_OF_RANKS; r += NUM_RANKS_PER_SHADOW_REG) {
		select_shadow_regs_for_update(r, write_group, 1);
		for (i = 0, p = test_bgn, d = 0; i < RW_MGR_MEM_DQ_PER_WRITE_DQS; i++, p++, d += delay_step) {
			DPRINT(1, "rw_mgr_mem_calibrate_vfifo_find_dqs_en_phase_sweep_dq_in_delay: g=%lu r=%lu, i=%lu p=%lu d=%lu",
			       write_group, r, i, p, d);
			scc_mgr_set_dq_out2_delay(write_group, i, d);
			scc_mgr_load_dq (i);
		}
		IOWR_32DIRECT (SCC_MGR_UPD, 0, 0);
	}
#endif
}

#if DDR3
// optimization used to recover some slots in ddr3 inst_rom
// could be applied to other protocols if we wanted to
void set_jump_as_return(void)
{
	// to save space, we replace return with jump to special shared RETURN instruction
	// so we set the counter to large value so that we always jump
	IOWR_32DIRECT (RW_MGR_LOAD_CNTR_0, 0, 0xFF);
	IOWR_32DIRECT (RW_MGR_LOAD_JUMP_ADD_0, 0, __RW_MGR_RETURN);

}
#endif

// should always use constants as argument to ensure all computations are performed at compile time
static inline void delay_for_n_mem_clocks(const alt_u32 clocks)
{
	alt_u32 afi_clocks;
	alt_u8 inner;
	alt_u8 outer;
	alt_u16 c_loop;

	TRACE_FUNC("clocks=%lu ... start", clocks);

	afi_clocks = (clocks + AFI_RATE_RATIO-1) / AFI_RATE_RATIO; /* scale (rounding up) to get afi clocks */

	// Note, we don't bother accounting for being off a little bit because of a few extra instructions in outer loops
	// Note, the loops have a test at the end, and do the test before the decrement, and so always perform the loop
	// 1 time more than the counter value
	if (afi_clocks == 0) {
		inner = outer = c_loop = 0;
	} else if (afi_clocks <= 0x100) {
		inner = afi_clocks-1;
		outer = 0;
		c_loop = 0;
	} else if (afi_clocks <= 0x10000) {
		inner = 0xff;
		outer = (afi_clocks-1) >> 8;
		c_loop = 0;
	} else {
		inner = 0xff;
		outer = 0xff;
		c_loop = (afi_clocks-1) >> 16;
	}

	// rom instructions are structured as follows:
	//
	//    IDLE_LOOP2: jnz cntr0, TARGET_A
	//    IDLE_LOOP1: jnz cntr1, TARGET_B
	//                return
	//
	// so, when doing nested loops, TARGET_A is set to IDLE_LOOP2, and TARGET_B is
	// set to IDLE_LOOP2 as well
	//
	// if we have no outer loop, though, then we can use IDLE_LOOP1 only, and set
	// TARGET_B to IDLE_LOOP1 and we skip IDLE_LOOP2 entirely
	//
	// a little confusing, but it helps save precious space in the inst_rom and sequencer rom
	// and keeps the delays more accurate and reduces overhead
	if (afi_clocks <= 0x100) {

		IOWR_32DIRECT (RW_MGR_LOAD_CNTR_1, 0, SKIP_DELAY_LOOP_VALUE_OR_ZERO(inner));
		IOWR_32DIRECT (RW_MGR_LOAD_JUMP_ADD_1, 0, __RW_MGR_IDLE_LOOP1);
		IOWR_32DIRECT (RW_MGR_RUN_SINGLE_GROUP, 0, __RW_MGR_IDLE_LOOP1);

	} else {
		IOWR_32DIRECT (RW_MGR_LOAD_CNTR_0, 0, SKIP_DELAY_LOOP_VALUE_OR_ZERO(inner));
		IOWR_32DIRECT (RW_MGR_LOAD_CNTR_1, 0, SKIP_DELAY_LOOP_VALUE_OR_ZERO(outer));
	
		IOWR_32DIRECT (RW_MGR_LOAD_JUMP_ADD_0, 0, __RW_MGR_IDLE_LOOP2);
		IOWR_32DIRECT (RW_MGR_LOAD_JUMP_ADD_1, 0, __RW_MGR_IDLE_LOOP2);

		// hack to get around compiler not being smart enough
		if (afi_clocks <= 0x10000) {
			// only need to run once
			IOWR_32DIRECT (RW_MGR_RUN_SINGLE_GROUP, 0, __RW_MGR_IDLE_LOOP2);
		} else {
			do {
				IOWR_32DIRECT (RW_MGR_RUN_SINGLE_GROUP, 0, __RW_MGR_IDLE_LOOP2);
			} while (c_loop-- != 0);
		}
	}

	TRACE_FUNC("clocks=%lu ... end", clocks);
}

// should always use constants as argument to ensure all computations are performed at compile time
static inline void delay_for_n_ns(const alt_u32 nanoseconds)
{
	TRACE_FUNC("nanoseconds=%lu ... end", nanoseconds);
	delay_for_n_mem_clocks((1000*nanoseconds) / (1000000/AFI_CLK_FREQ) * AFI_RATE_RATIO);
}

#if RLDRAM3
// Special routine to recover memory device from illegal state after
// ck/dk relationship is potentially violated.
static inline void recover_mem_device_after_ck_dqs_violation(void)
{
	//USER Issue MRS0 command. For some reason this is required once we
	//USER violate tCKDK. Without this all subsequent write tests will fail
	//USER even with known good delays.
   
   //USER Load MR0
	if ( RW_MGR_MEM_NUMBER_OF_RANKS == 1 ) {
		IOWR_32DIRECT (RW_MGR_SET_CS_AND_ODT_MASK, 0, 0xFE);
		IOWR_32DIRECT (RW_MGR_RUN_SINGLE_GROUP, 0, __RW_MGR_MRS0);
	} else if ( RW_MGR_MEM_NUMBER_OF_RANKS == 2 ) {
		IOWR_32DIRECT (RW_MGR_SET_CS_AND_ODT_MASK, 0, 0xFC);
		IOWR_32DIRECT (RW_MGR_RUN_SINGLE_GROUP, 0, __RW_MGR_MRS0);
	} else if ( RW_MGR_MEM_NUMBER_OF_RANKS == 4 ) {
		IOWR_32DIRECT (RW_MGR_SET_CS_AND_ODT_MASK, 0, 0xFC);
		IOWR_32DIRECT (RW_MGR_RUN_SINGLE_GROUP, 0, __RW_MGR_MRS0);
		//USER Wait MRSC
		delay_for_n_mem_clocks(12);
		IOWR_32DIRECT (RW_MGR_SET_CS_AND_ODT_MASK, 0, 0xF3);
		IOWR_32DIRECT (RW_MGR_RUN_SINGLE_GROUP, 0, __RW_MGR_MRS0_QUAD_RANK);
	}
	else {
		IOWR_32DIRECT (RW_MGR_SET_CS_AND_ODT_MASK, 0, 0xFE);
		IOWR_32DIRECT (RW_MGR_RUN_SINGLE_GROUP, 0, __RW_MGR_MRS0);
	}

	//USER Wait MRSC
	delay_for_n_mem_clocks(12);
}
#else
// Special routine to recover memory device from illegal state after
// ck/dqs relationship is violated.
static inline void recover_mem_device_after_ck_dqs_violation(void)
{
	// Current protocol doesn't require any special recovery
}
#endif

#if (LRDIMM && DDR3)
// Routine to program specific LRDIMM control words.
static void rw_mgr_lrdimm_rc_program(alt_u32 fscw, alt_u32 rc_addr, alt_u32 rc_val)
{
	alt_u32 i;
	const alt_u32 AC_BASE_CONTENT = __RW_MGR_CONTENT_ac_rdimm;
	//USER These values should be dynamically loaded instead of hard-coded
	const alt_u32 AC_ADDRESS_POSITION = 0x0;
	const alt_u32 AC_BANK_ADDRESS_POSITION = 0xD;
	alt_u32 ac_content;
	alt_u32 lrdimm_cs_msk = RW_MGR_RANK_NONE;

	TRACE_FUNC();

	//USER Turn on only CS0 and CS1 for each DIMM.
	for (i = 0; i < RW_MGR_MEM_CHIP_SELECT_WIDTH; i+= RW_MGR_MEM_NUMBER_OF_CS_PER_DIMM)
	{
		lrdimm_cs_msk &= (~(3 << i));
	}

	IOWR_32DIRECT (RW_MGR_SET_CS_AND_ODT_MASK, 0, lrdimm_cs_msk);

	// Program the fscw first (RC7), followed by the actual value
	for (i = 0; i < 2; i++)
	{
		alt_u32 addr;
		alt_u32 val;

		addr = (i == 0) ? 7 : rc_addr;
		val = (i == 0) ? fscw : rc_val;

		ac_content =
			AC_BASE_CONTENT |
			//USER Word address
			((addr & 0x7) << AC_ADDRESS_POSITION) |
			(((addr >> 3) & 0x1) << (AC_BANK_ADDRESS_POSITION + 2)) |
			//USER Configuration Word
			(((val >> 2) & 0x3) << (AC_BANK_ADDRESS_POSITION)) |
			((val & 0x3) << (AC_ADDRESS_POSITION + 3));

		//USER Override the AC row with the RDIMM command
		IOWR_32DIRECT(BASE_RW_MGR, 0x1C00 + (__RW_MGR_ac_rdimm << 2), ac_content);

		set_jump_as_return();
		IOWR_32DIRECT (RW_MGR_RUN_SINGLE_GROUP, 0, __RW_MGR_RDIMM_CMD);
	}

	// USER The following registers require a delay of tSTAB (6us) for proper functionality.
	// USER F0RC2, F0RC10, F0RC11, F1RC8, F1RC11-F1RC15
	// USER Note that it is only necessary to wait tSTAB after all of these
	// USER control words have been written, not after each one. Only F0RC0-F0RC15
	// USER are guaranteed to be written (and in order), but F1* are not so
	// USER wait after each.
	if (    ((fscw == 0) && ((rc_addr==2) || (rc_addr==10) || (rc_addr==11)))
		  || ((fscw == 1) && (rc_addr >= 8)))
	{
		delay_for_n_ns(6000);
	}
}
#endif
#if (RDIMM || LRDIMM) && DDR3
void rw_mgr_rdimm_initialize(void)
{
	alt_u32 i;
	alt_u32 conf_word;
#if RDIMM
	const alt_u32 AC_BASE_CONTENT = __RW_MGR_CONTENT_ac_rdimm;
	//USER These values should be dynamically loaded instead of hard-coded
	const alt_u32 AC_ADDRESS_POSITION = 0x0;
	const alt_u32 AC_BANK_ADDRESS_POSITION = 0xD;
	alt_u32 ac_content;
#endif

	TRACE_FUNC();
	
	//USER RDIMM registers are programmed by writing 16 configuration words
	//USER 1. An RDIMM command is a NOP with all CS asserted
	//USER 2. The 4-bit address of the configuration words is 
	//USER    * { mem_ba[2] , mem_a[2] , mem_a[1] , mem_a[0] }
	//USER 3. The 4-bit configuration word is
	//USER    * { mem_ba[1] , mem_ba[0] , mem_a[4] , mem_a[3] }

#if RDIMM
	//USER Turn on all ranks
	IOWR_32DIRECT (RW_MGR_SET_CS_AND_ODT_MASK, 0, RW_MGR_RANK_ALL);
#endif

	for(i = 0; i < 16; i++)
	{
	

		if(i < 8)
		{
#if ENABLE_TCL_DEBUG && USE_USER_RDIMM_VALUE
			conf_word = (my_debug_data.command_parameters[0] >> (i * 4)) & 0xF;		
#else			
			conf_word = (RDIMM_CONFIG_WORD_LOW >> (i * 4)) & 0xF;	
#endif			
		}
		else
		{
#if ENABLE_TCL_DEBUG && USE_USER_RDIMM_VALUE	
			conf_word = (my_debug_data.command_parameters[1] >> ((i - 8) * 4)) & 0xF;	
#else			
			conf_word = (RDIMM_CONFIG_WORD_HIGH >> ((i - 8) * 4)) & 0xF;			
#endif		
		}	

#if RDIMM
		ac_content = 
			AC_BASE_CONTENT | 
			//USER Word address
			((i & 0x7) << AC_ADDRESS_POSITION) |
			(((i >> 3) & 0x1) << (AC_BANK_ADDRESS_POSITION + 2)) |
			//USER Configuration Word
			(((conf_word >> 2) & 0x3) << (AC_BANK_ADDRESS_POSITION)) |
			((conf_word & 0x3) << (AC_ADDRESS_POSITION + 3));

		//USER Override the AC row with the RDIMM command
		IOWR_32DIRECT(BASE_RW_MGR, 0x1C00 + (__RW_MGR_ac_rdimm << 2), ac_content);

		set_jump_as_return();
		IOWR_32DIRECT (RW_MGR_RUN_SINGLE_GROUP, 0, __RW_MGR_RDIMM_CMD);
		//USER When sending the RC2 or RC10 word, tSTAB time must elapse before the next command
		//USER is sent out. tSTAB is currently hard-coded to 6us.
		if((i == 2) || (i == 10))
		{
			//USER tSTAB = 6 us
			delay_for_n_ns(6000);
		}

#endif
#if LRDIMM
		// USER Program configuration word with FSCW set to zero.
		rw_mgr_lrdimm_rc_program(0, i, conf_word);
#endif
	}
}
#else
void rw_mgr_rdimm_initialize(void) { }
#endif

#if DDR3

#if LRDIMM
alt_u32 ddr3_mirror_mrs_cmd(alt_u32 bit_vector) {
	// This function performs address mirroring of an AC ROM command, which
	// requires swapping the following DDR3 bits:
	//     A[3] <=> A[4]
	//     A[5] <=> A[6]
	//     A[7] <=> A[8]
	//    BA[0] <=>BA[1]
	// We assume AC_ROM_ENTRY = {BA[2:0], A[15:0]}.
	alt_u32 unchanged_bits;
	alt_u32 mask_a;
	alt_u32 mask_b;
	alt_u32 retval;

	unchanged_bits = (~(DDR3_AC_MIRR_MASK | (DDR3_AC_MIRR_MASK << 1))) & bit_vector;
	mask_a = DDR3_AC_MIRR_MASK & bit_vector;
	mask_b = (DDR3_AC_MIRR_MASK << 1) & bit_vector;

	retval = unchanged_bits | (mask_a << 1) | (mask_b >> 1);

	return retval;
}

void rtt_change_MRS1_MRS2_NOM_WR (alt_u32 prev_ac_mr , alt_u32 odt_ac_mr, alt_u32 mirr_on, alt_u32 mr_cmd ) {
	// This function updates the ODT-specific Mode Register bits (MRS1 or MRS2) in the AC ROM.
	// Parameters:  prev_ac_mr - Original, *un-mirrored* AC ROM Entry
	//              odt_ac_mr  - ODT bits to update (un-mirrored)
	//              mirr_on    - boolean flag indicating if the regular or mirrored entry is updated
	//              mr_cmd     - Mode register command (only MR1 and MR2 are supported for DDR3)
	alt_u32 new_ac_mr;
	alt_u32 ac_rom_entry = 0;
	alt_u32 ac_rom_mask;

	switch (mr_cmd) {
		case 1: {
			// USER MRS1 = RTT_NOM, RTT_DRV
			ac_rom_mask = DDR3_MR1_ODT_MASK;
			ac_rom_entry = mirr_on ? (0x1C00 | (__RW_MGR_ac_mrs1_mirr << 2))
			                       : (0x1C00 | (__RW_MGR_ac_mrs1 << 2));
		} break;
		case 2: {
			// USER MRS2 = RTT_WR
			ac_rom_mask = DDR3_MR2_ODT_MASK;
			ac_rom_entry = mirr_on ? (0x1C00 | (__RW_MGR_ac_mrs2_mirr << 2))
			                       : (0x1C00 | (__RW_MGR_ac_mrs2 << 2));
		} break;
	}

	// USER calculate new AC values and update ROM
	new_ac_mr  = odt_ac_mr;
	new_ac_mr |= (prev_ac_mr & ac_rom_mask);
	if (mirr_on) {
		new_ac_mr = ddr3_mirror_mrs_cmd(new_ac_mr);
	}
	IOWR_32DIRECT(BASE_RW_MGR, ac_rom_entry, new_ac_mr);
}
#endif //LRDIMM

void rw_mgr_mem_initialize (void)
{
	alt_u32 r;

#if LRDIMM
	alt_u32 rtt_nom;
	alt_u32 rtt_drv;
	alt_u32 rtt_wr;
#endif // LRDIMM

	TRACE_FUNC();

	//USER The reset / cke part of initialization is broadcasted to all ranks
	IOWR_32DIRECT (RW_MGR_SET_CS_AND_ODT_MASK, 0, RW_MGR_RANK_ALL);

	// Here's how you load register for a loop
	//USER Counters are located @ 0x800
	//USER Jump address are located @ 0xC00
	//USER For both, registers 0 to 3 are selected using bits 3 and 2, like in
	//USER 0x800, 0x804, 0x808, 0x80C and 0xC00, 0xC04, 0xC08, 0xC0C
	// I know this ain't pretty, but Avalon bus throws away the 2 least significant bits
	
	//USER start with memory RESET activated

	//USER tINIT is typically 200us (but can be adjusted in the GUI)
	//USER The total number of cycles required for this nested counter structure to
	//USER complete is defined by:
	//USER        num_cycles = (CTR2 + 1) * [(CTR1 + 1) * (2 * (CTR0 + 1) + 1) + 1] + 1

	//USER Load counters
	IOWR_32DIRECT (RW_MGR_LOAD_CNTR_0, 0, SKIP_DELAY_LOOP_VALUE_OR_ZERO(SEQ_TINIT_CNTR0_VAL));
	IOWR_32DIRECT (RW_MGR_LOAD_CNTR_1, 0, SKIP_DELAY_LOOP_VALUE_OR_ZERO(SEQ_TINIT_CNTR1_VAL));
	IOWR_32DIRECT (RW_MGR_LOAD_CNTR_2, 0, SKIP_DELAY_LOOP_VALUE_OR_ZERO(SEQ_TINIT_CNTR2_VAL));
	
	//USER Load jump address
	IOWR_32DIRECT (RW_MGR_LOAD_JUMP_ADD_0, 0, __RW_MGR_INIT_RESET_0_CKE_0);
	IOWR_32DIRECT (RW_MGR_LOAD_JUMP_ADD_1, 0, __RW_MGR_INIT_RESET_0_CKE_0);
	IOWR_32DIRECT (RW_MGR_LOAD_JUMP_ADD_2, 0, __RW_MGR_INIT_RESET_0_CKE_0);

	//USER Execute count instruction
	IOWR_32DIRECT (RW_MGR_RUN_SINGLE_GROUP, 0, __RW_MGR_INIT_RESET_0_CKE_0);

	//USER indicate that memory is stable
	IOWR_32DIRECT (PHY_MGR_RESET_MEM_STBL, 0, 1);

	//USER transition the RESET to high 
	//USER Wait for 500us
	//USER        num_cycles = (CTR2 + 1) * [(CTR1 + 1) * (2 * (CTR0 + 1) + 1) + 1] + 1
	//USER Load counters
	IOWR_32DIRECT (RW_MGR_LOAD_CNTR_0, 0, SKIP_DELAY_LOOP_VALUE_OR_ZERO(SEQ_TRESET_CNTR0_VAL));
	IOWR_32DIRECT (RW_MGR_LOAD_CNTR_1, 0, SKIP_DELAY_LOOP_VALUE_OR_ZERO(SEQ_TRESET_CNTR1_VAL));
	IOWR_32DIRECT (RW_MGR_LOAD_CNTR_2, 0, SKIP_DELAY_LOOP_VALUE_OR_ZERO(SEQ_TRESET_CNTR2_VAL));

	//USER Load jump address
	IOWR_32DIRECT (RW_MGR_LOAD_JUMP_ADD_0, 0, __RW_MGR_INIT_RESET_1_CKE_0);
	IOWR_32DIRECT (RW_MGR_LOAD_JUMP_ADD_1, 0, __RW_MGR_INIT_RESET_1_CKE_0);
	IOWR_32DIRECT (RW_MGR_LOAD_JUMP_ADD_2, 0, __RW_MGR_INIT_RESET_1_CKE_0);

	IOWR_32DIRECT (RW_MGR_RUN_SINGLE_GROUP, 0, __RW_MGR_INIT_RESET_1_CKE_0);

	//USER bring up clock enable 

	//USER tXRP < 250 ck cycles
	delay_for_n_mem_clocks(250);

#ifdef RDIMM
	// USER initialize RDIMM buffer so MRS and RZQ Calibrate commands will be 
	// USER propagated to discrete memory devices
	rw_mgr_rdimm_initialize();
#endif

#if LRDIMM
	// USER initialize LRDIMM MB so MRS and RZQ Calibrate commands will be 
	// USER propagated to all sub-ranks.  Per LRDIMM spec, all LRDIMM ranks must have
	// USER RTT_WR set, but only physical ranks 0 and 1 should have RTT_NOM set.
	// USER Therefore RTT_NOM=0 is broadcast to all ranks, and the non-zero value is 
	// USER programmed directly into Ranks 0 and 1 using physical MRS targetting.
	rw_mgr_rdimm_initialize();

	rtt_nom = LRDIMM_SPD_MR_RTT_NOM(LRDIMM_SPD_MR);
	rtt_drv = LRDIMM_SPD_MR_RTT_DRV(LRDIMM_SPD_MR);
	rtt_wr  = LRDIMM_SPD_MR_RTT_WR(LRDIMM_SPD_MR);

	// USER Configure LRDIMM to broadcast LRDIMM MRS commands to all ranks
	rw_mgr_lrdimm_rc_program(0, 14, (((RDIMM_CONFIG_WORD_HIGH >> 24) & 0xF) & (~0x4)));

	// USER Update contents of AC ROM with new RTT WR, DRV values only (NOM = Off)
	rtt_change_MRS1_MRS2_NOM_WR(__RW_MGR_CONTENT_ac_mrs1, rtt_drv, 0, 1);
	rtt_change_MRS1_MRS2_NOM_WR(__RW_MGR_CONTENT_ac_mrs1, rtt_drv, 1, 1);
	rtt_change_MRS1_MRS2_NOM_WR(__RW_MGR_CONTENT_ac_mrs2, rtt_wr,  0, 2);
	rtt_change_MRS1_MRS2_NOM_WR(__RW_MGR_CONTENT_ac_mrs2, rtt_wr,  1, 2);
#endif
#if RDIMM
	// USER initialize RDIMM buffer so MRS and RZQ Calibrate commands will be 
	// USER propagated to discrete memory devices
	rw_mgr_rdimm_initialize();
#endif

	for (r = 0; r < RW_MGR_MEM_NUMBER_OF_RANKS; r++) {
		if (param->skip_ranks[r]) {
			//USER request to skip the rank

			continue;
		}

		//USER set rank 
#if MRS_MIRROR_PING_PONG_ATSO
		// Special case
		// SIDE 0
		set_rank_and_odt_mask_for_ping_pong_atso(0, RW_MGR_ODT_MODE_OFF);
		set_jump_as_return();
		IOWR_32DIRECT (RW_MGR_RUN_SINGLE_GROUP, 0, __RW_MGR_MRS2);
		delay_for_n_mem_clocks(4);
		set_jump_as_return();
		IOWR_32DIRECT (RW_MGR_RUN_SINGLE_GROUP, 0, __RW_MGR_MRS3);
		delay_for_n_mem_clocks(4);
		set_jump_as_return();
		IOWR_32DIRECT (RW_MGR_RUN_SINGLE_GROUP, 0, __RW_MGR_MRS1);
		set_jump_as_return();
		IOWR_32DIRECT (RW_MGR_RUN_SINGLE_GROUP, 0, __RW_MGR_MRS0_DLL_RESET);

		// SIDE 1
		set_rank_and_odt_mask_for_ping_pong_atso(1, RW_MGR_ODT_MODE_OFF);
		set_jump_as_return();
		IOWR_32DIRECT (RW_MGR_RUN_SINGLE_GROUP, 0, __RW_MGR_MRS2_MIRR);
		delay_for_n_mem_clocks(4);
		set_jump_as_return();
		IOWR_32DIRECT (RW_MGR_RUN_SINGLE_GROUP, 0, __RW_MGR_MRS3_MIRR);
		delay_for_n_mem_clocks(4);
		set_jump_as_return();
		IOWR_32DIRECT (RW_MGR_RUN_SINGLE_GROUP, 0, __RW_MGR_MRS1_MIRR);
		delay_for_n_mem_clocks(4);
		set_jump_as_return();
		IOWR_32DIRECT (RW_MGR_RUN_SINGLE_GROUP, 0, __RW_MGR_MRS0_DLL_RESET_MIRR);

		// Unmask all CS
		set_rank_and_odt_mask(r, RW_MGR_ODT_MODE_OFF);
#else
		set_rank_and_odt_mask(r, RW_MGR_ODT_MODE_OFF);

		//USER Use Mirror-ed commands for odd ranks if address mirrorring is on
		if((RW_MGR_MEM_ADDRESS_MIRRORING >> r) & 0x1) {
			set_jump_as_return();
			IOWR_32DIRECT (RW_MGR_RUN_SINGLE_GROUP, 0, __RW_MGR_MRS2_MIRR);
			delay_for_n_mem_clocks(4);
			set_jump_as_return();
			IOWR_32DIRECT (RW_MGR_RUN_SINGLE_GROUP, 0, __RW_MGR_MRS3_MIRR);
			delay_for_n_mem_clocks(4);
			set_jump_as_return();
			IOWR_32DIRECT (RW_MGR_RUN_SINGLE_GROUP, 0, __RW_MGR_MRS1_MIRR);
			delay_for_n_mem_clocks(4);
			set_jump_as_return();
			IOWR_32DIRECT (RW_MGR_RUN_SINGLE_GROUP, 0, __RW_MGR_MRS0_DLL_RESET_MIRR);
		} else {
			set_jump_as_return();
			IOWR_32DIRECT (RW_MGR_RUN_SINGLE_GROUP, 0, __RW_MGR_MRS2);
			delay_for_n_mem_clocks(4);
			set_jump_as_return();
			IOWR_32DIRECT (RW_MGR_RUN_SINGLE_GROUP, 0, __RW_MGR_MRS3);
			delay_for_n_mem_clocks(4);
			set_jump_as_return();
			IOWR_32DIRECT (RW_MGR_RUN_SINGLE_GROUP, 0, __RW_MGR_MRS1);
			set_jump_as_return();
			IOWR_32DIRECT (RW_MGR_RUN_SINGLE_GROUP, 0, __RW_MGR_MRS0_DLL_RESET);
		}
#endif

		set_jump_as_return();
		IOWR_32DIRECT (RW_MGR_RUN_SINGLE_GROUP, 0, __RW_MGR_ZQCL);

		//USER tZQinit = tDLLK = 512 ck cycles
		delay_for_n_mem_clocks(512);
	}
#if LRDIMM
	// USER Configure LRDIMM to target physical ranks decoded by RM bits only (ranks 0,1 only)
	// USER Set bit F0RC14.DBA0 to '1' so MRS commands target physical ranks only
	rw_mgr_lrdimm_rc_program(0, 14, (((RDIMM_CONFIG_WORD_HIGH >> 24) & 0xF) | 0x4));
	// USER update AC ROM MR1 entry to include RTT_NOM
	rtt_change_MRS1_MRS2_NOM_WR(__RW_MGR_CONTENT_ac_mrs1, (rtt_drv|rtt_nom), 0, 1);
	rtt_change_MRS1_MRS2_NOM_WR(__RW_MGR_CONTENT_ac_mrs1, (rtt_drv|rtt_nom), 1, 1);
	for (r = 0; r < RW_MGR_MEM_NUMBER_OF_RANKS; r++) {
		if (param->skip_ranks[r]) {
			//USER request to skip the rank
			continue;
		}

		//USER set rank 
		set_rank_and_odt_mask(r, RW_MGR_ODT_MODE_OFF);

		//USER Use Mirror-ed commands for odd ranks if address mirrorring is on
		if((RW_MGR_MEM_ADDRESS_MIRRORING >> r) & 0x1) {
			delay_for_n_mem_clocks(4);
			set_jump_as_return();
			IOWR_32DIRECT (RW_MGR_RUN_SINGLE_GROUP, 0, __RW_MGR_MRS1_MIRR);
			delay_for_n_mem_clocks(4);
		} else {
			delay_for_n_mem_clocks(4);
			set_jump_as_return();
			IOWR_32DIRECT (RW_MGR_RUN_SINGLE_GROUP, 0, __RW_MGR_MRS1);
			delay_for_n_mem_clocks(4);
		}
	}

	// USER Initiate LRDIMM MB->Physical Rank training here
	// USER -> Set minimum skew mode for levelling - F3RC6 = 0001
	rw_mgr_lrdimm_rc_program(3, 6, 0x1);
	// USER -> Set error status output in register F2RC3 for debugging purposes
	rw_mgr_lrdimm_rc_program(2, 3, 0x8);

#ifdef LRDIMM_EXT_CONFIG_ARRAY
	// USER Configure LRDIMM ODT/Drive parameters using SPD information
	{
		static const alt_u8 lrdimm_cfg_array[][3] = LRDIMM_EXT_CONFIG_ARRAY;
		alt_u32 cfg_reg_ctr;

		for (cfg_reg_ctr = 0; cfg_reg_ctr < (sizeof(lrdimm_cfg_array)/sizeof(lrdimm_cfg_array[0])); cfg_reg_ctr++)
		{
			alt_u32 lrdimm_fp  = (alt_u32)lrdimm_cfg_array[cfg_reg_ctr][0];
			alt_u32 lrdimm_rc  = (alt_u32)lrdimm_cfg_array[cfg_reg_ctr][1];
			alt_u32 lrdimm_val = (alt_u32)lrdimm_cfg_array[cfg_reg_ctr][2];

			rw_mgr_lrdimm_rc_program(lrdimm_fp, lrdimm_rc, lrdimm_val);
		}
	}
#endif // LRDIMM_EXT_CONFIG_ARRAY

	// USER -> Initiate MB->DIMM training on the LRDIMM
	rw_mgr_lrdimm_rc_program(0, 12, 0x2);
#if (!STATIC_SKIP_DELAY_LOOPS)
	// USER Wait for max(tcal) * number of physical ranks. Tcal is approx. 10ms.
	for (r = 0; r < RW_MGR_MEM_NUMBER_OF_RANKS * RW_MGR_MEM_NUMBER_OF_CS_PER_DIMM; r++)
	{
		delay_for_n_ns(80000000UL);
	}
#endif // !STATIC_SKIP_DELAY_LOOPS
	// USER Place MB back in normal operating mode
	rw_mgr_lrdimm_rc_program(0, 12, 0x0);
#endif // LRDIMM
}
#if ENABLE_NON_DESTRUCTIVE_CALIB
void rw_mgr_mem_initialize_no_init (void)
{
	alt_u32 r;
	alt_u32 mem_refresh_all_ranks(alt_u32 no_validate);
	TRACE_FUNC();
	rw_mgr_rdimm_initialize();
	IOWR_32DIRECT (RW_MGR_SET_CS_AND_ODT_MASK, 0, RW_MGR_RANK_ALL);
	IOWR_32DIRECT (RW_MGR_RUN_SINGLE_GROUP, 0, __RW_MGR_RETURN);
	delay_for_n_mem_clocks(512);
	mem_refresh_all_ranks(1);
	IOWR_32DIRECT (PHY_MGR_RESET_MEM_STBL, 0, 1);
	for (r = 0; r < RW_MGR_MEM_NUMBER_OF_RANKS; r++) {
		if (param->skip_ranks[r]) {
			continue;
		}
		set_rank_and_odt_mask(r, RW_MGR_ODT_MODE_OFF);
		set_jump_as_return();
		if((RW_MGR_MEM_ADDRESS_MIRRORING >> r) & 0x1) {
			IOWR_32DIRECT (RW_MGR_RUN_SINGLE_GROUP, 0, __RW_MGR_MRS0_DLL_RESET_MIRR);
		} else {
			IOWR_32DIRECT (RW_MGR_RUN_SINGLE_GROUP, 0, __RW_MGR_MRS0_DLL_RESET);
		}
		delay_for_n_mem_clocks(4);
		set_jump_as_return();
		IOWR_32DIRECT (RW_MGR_RUN_SINGLE_GROUP, 0, __RW_MGR_ZQCL);
		delay_for_n_mem_clocks(512);
	}
}
#endif
#endif // DDR3

#if DDR2
void rw_mgr_mem_initialize (void)
{
	alt_u32 r;

	TRACE_FUNC();
	
	//USER *** NOTE ***
	//USER The following STAGE (n) notation refers to the corresponding stage in the Micron datasheet

	// Here's how you load register for a loop
	//USER Counters are located @ 0x800
	//USER Jump address are located @ 0xC00
	//USER For both, registers 0 to 3 are selected using bits 3 and 2, like in
	//USER 0x800, 0x804, 0x808, 0x80C and 0xC00, 0xC04, 0xC08, 0xC0C
	// I know this ain't pretty, but Avalon bus throws away the 2 least significant bits
	
	//USER *** STAGE (1, 2, 3) ***

	//USER start with CKE low 

	//USER tINIT is typically 200us (but can be adjusted in the GUI)
	//USER The total number of cycles required for this nested counter structure to
	//USER complete is defined by:
	//USER        num_cycles = (CTR0 + 1) * [(CTR1 + 1) * (2 * (CTR2 + 1) + 1) + 1] + 1

	//TODO: Need to manage multi-rank

	//USER Load counters
	IOWR_32DIRECT (RW_MGR_LOAD_CNTR_0, 0, SKIP_DELAY_LOOP_VALUE_OR_ZERO(SEQ_TINIT_CNTR0_VAL));
	IOWR_32DIRECT (RW_MGR_LOAD_CNTR_1, 0, SKIP_DELAY_LOOP_VALUE_OR_ZERO(SEQ_TINIT_CNTR1_VAL));
	IOWR_32DIRECT (RW_MGR_LOAD_CNTR_2, 0, SKIP_DELAY_LOOP_VALUE_OR_ZERO(SEQ_TINIT_CNTR2_VAL));
	
	//USER Load jump address
	IOWR_32DIRECT (RW_MGR_LOAD_JUMP_ADD_0, 0, __RW_MGR_INIT_CKE_0);
	IOWR_32DIRECT (RW_MGR_LOAD_JUMP_ADD_1, 0, __RW_MGR_INIT_CKE_0);
	IOWR_32DIRECT (RW_MGR_LOAD_JUMP_ADD_2, 0, __RW_MGR_INIT_CKE_0);

	//USER Execute count instruction
	IOWR_32DIRECT (RW_MGR_RUN_SINGLE_GROUP, 0, __RW_MGR_INIT_CKE_0);

	//USER indicate that memory is stable 
	IOWR_32DIRECT (PHY_MGR_RESET_MEM_STBL, 0, 1);

	//USER Bring up CKE 
	IOWR_32DIRECT (RW_MGR_RUN_SINGLE_GROUP, 0, __RW_MGR_NOP);

	//USER *** STAGE (4)

	//USER Wait for 400ns 
	delay_for_n_ns(400);

	//USER Multi-rank section begins here
	for (r = 0; r < RW_MGR_MEM_NUMBER_OF_RANKS; r++) {
		if (param->skip_ranks[r]) {
			//USER request to skip the rank

			continue;
		}

		//USER set rank 
		set_rank_and_odt_mask(r, RW_MGR_ODT_MODE_OFF);

		//USER * **** *
		//USER * NOTE *
		//USER * **** *
		//USER The following commands must be spaced by tMRD or tRPA which are in the order
		//USER of 2 to 4 full rate cycles. This is peanuts in the NIOS domain, so for now
		//USER we can avoid redundant wait loops

		// Possible FIXME BEN: for HHP, we need to add delay loops to be sure
		// although, the sequencer write interface by itself likely has enough delay

		IOWR_32DIRECT (RW_MGR_RUN_SINGLE_GROUP, 0, __RW_MGR_PRECHARGE_ALL);

		//USER *** STAGE (5)
		IOWR_32DIRECT (RW_MGR_RUN_SINGLE_GROUP, 0, __RW_MGR_EMR2);

		//USER *** STAGE (6)
		IOWR_32DIRECT (RW_MGR_RUN_SINGLE_GROUP, 0, __RW_MGR_EMR3);

		//USER *** STAGE (7)
		IOWR_32DIRECT (RW_MGR_RUN_SINGLE_GROUP, 0, __RW_MGR_EMR);

		//USER *** STAGE (8)
		//USER DLL reset
		IOWR_32DIRECT (RW_MGR_RUN_SINGLE_GROUP, 0, __RW_MGR_MR_DLL_RESET);

		//USER *** STAGE (9)
		IOWR_32DIRECT (RW_MGR_RUN_SINGLE_GROUP, 0, __RW_MGR_PRECHARGE_ALL);

		//USER *** STAGE (10)

		//USER Issue 2 refresh commands spaced by tREF 

		//USER First REFRESH
		IOWR_32DIRECT (RW_MGR_RUN_SINGLE_GROUP, 0, __RW_MGR_REFRESH);

		//USER tREF = 200ns
		delay_for_n_ns(200);

		//USER Second REFRESH
		IOWR_32DIRECT (RW_MGR_RUN_SINGLE_GROUP, 0, __RW_MGR_REFRESH);

		//USER Second idle loop
		delay_for_n_ns(200);

		//USER *** STAGE (11)
		IOWR_32DIRECT (RW_MGR_RUN_SINGLE_GROUP, 0, __RW_MGR_MR_CALIB);

		//USER *** STAGE (12)
		//USER OCD defaults
		IOWR_32DIRECT (RW_MGR_RUN_SINGLE_GROUP, 0, __RW_MGR_EMR_OCD_ENABLE);

		//USER *** STAGE (13)
		//USER OCD exit
		IOWR_32DIRECT (RW_MGR_RUN_SINGLE_GROUP, 0, __RW_MGR_EMR);

		//USER *** STAGE (14)

		//USER The memory is now initialized. Before being able to use it, we must still
		//USER wait for the DLL to lock, 200 clock cycles after it was reset @ STAGE (8).
		//USER Since we cannot keep track of time in any other way, let's start counting from now
		delay_for_n_mem_clocks(200);
	}
}
#endif // DDR2 

#if LPDDR2
void rw_mgr_mem_initialize (void)
{
	alt_u32 r;

	//USER *** NOTE ***
	//USER The following STAGE (n) notation refers to the corresponding stage in the Micron datasheet

	// Here's how you load register for a loop
	//USER Counters are located @ 0x800
	//USER Jump address are located @ 0xC00
	//USER For both, registers 0 to 3 are selected using bits 3 and 2, like in
	//USER 0x800, 0x804, 0x808, 0x80C and 0xC00, 0xC04, 0xC08, 0xC0C
	// I know this ain't pretty, but Avalon bus throws away the 2 least significant bits
	
	//USER *** STAGE (1, 2, 3) ***

	//USER start with CKE low 

	//USER tINIT1 = 100ns

	//USER 100ns @ 300MHz (3.333 ns) ~ 30 cycles
	//USER If a is the number of iteration in a loop
	//USER it takes the following number of cycles to complete the operation:
	//USER number_of_cycles = (2 + n) * a
	//USER where n is the number of instruction in the inner loop
	//USER One possible solution is n = 0 , a = 15 => a = 0x10

	//USER Load counter
	IOWR_32DIRECT (RW_MGR_LOAD_CNTR_0, 0, SKIP_DELAY_LOOP_VALUE_OR_ZERO(0x10));
	
	//USER Load jump address
	IOWR_32DIRECT (RW_MGR_LOAD_JUMP_ADD_0, 0, __RW_MGR_INIT_CKE_0);

	//USER Execute count instruction
	IOWR_32DIRECT (RW_MGR_RUN_SINGLE_GROUP, 0, __RW_MGR_INIT_CKE_0);

	//USER tINIT3 = 200us
	delay_for_n_ns(200000);

	//USER indicate that memory is stable 
	IOWR_32DIRECT (PHY_MGR_RESET_MEM_STBL, 0, 1);

	//USER Multi-rank section begins here
	for (r = 0; r < RW_MGR_MEM_NUMBER_OF_RANKS; r++) {
		if (param->skip_ranks[r]) {
			//USER request to skip the rank

			continue;
		}

		//USER set rank 
		set_rank_and_odt_mask(r, RW_MGR_ODT_MODE_OFF);

		//USER MRW RESET
		IOWR_32DIRECT (RW_MGR_RUN_SINGLE_GROUP, 0, __RW_MGR_MR63_RESET);
	}

	//USER tINIT5 = 10us
	delay_for_n_ns(10000);

	//USER Multi-rank section begins here
	for (r = 0; r < RW_MGR_MEM_NUMBER_OF_RANKS; r++) {
		if (param->skip_ranks[r]) {
			//USER request to skip the rank

			continue;
		}

		//USER set rank 
		set_rank_and_odt_mask(r, RW_MGR_ODT_MODE_OFF);

		//USER MRW ZQC
		// Note: We cannot calibrate other ranks when the current rank is calibrating for tZQINIT
		IOWR_32DIRECT (RW_MGR_RUN_SINGLE_GROUP, 0, __RW_MGR_MR10_ZQC);

		//USER tZQINIT = 1us
		delay_for_n_ns(1000);

		//USER * **** *
		//USER * NOTE *
		//USER * **** *
		//USER The following commands must be spaced by tMRW which is in the order
		//USER of 3 to 5 full rate cycles. This is peanuts in the NIOS domain, so for now
		//USER we can avoid redundant wait loops

		//USER MRW MR1
		IOWR_32DIRECT (RW_MGR_RUN_SINGLE_GROUP, 0, __RW_MGR_MR1_CALIB);

		//USER MRW MR2
		IOWR_32DIRECT (RW_MGR_RUN_SINGLE_GROUP, 0, __RW_MGR_MR2);

		//USER MRW MR3
		IOWR_32DIRECT (RW_MGR_RUN_SINGLE_GROUP, 0, __RW_MGR_MR3);
	}
}
#endif // LPDDR2 

#if LPDDR1
void rw_mgr_mem_initialize (void)
{
	alt_u32 r;

	TRACE_FUNC();
	
	//USER *** NOTE ***
	//USER The following STAGE (n) notation refers to the corresponding stage in the Micron datasheet

	// Here's how you load register for a loop
	//USER Counters are located @ 0x800
	//USER Jump address are located @ 0xC00
	//USER For both, registers 0 to 3 are selected using bits 3 and 2, like in
	//USER 0x800, 0x804, 0x808, 0x80C and 0xC00, 0xC04, 0xC08, 0xC0C
	// I know this ain't pretty, but Avalon bus throws away the 2 least significant bits
	
	//USER *** STAGE (1, 2, 3) ***

	//USER start with CKE high 

	//USER tINIT = 200us

	//USER 200us @ 300MHz (3.33 ns) ~ 60000 clock cycles
	//USER If a and b are the number of iteration in 2 nested loops
	//USER it takes the following number of cycles to complete the operation:
	//USER number_of_cycles = ((2 + n) * b + 2) * a
	//USER where n is the number of instruction in the inner loop
	//USER One possible solution is n = 0 , a = 256 , b = 118 => a = FF, b = 76

	//TODO: Need to manage multi-rank

	//USER Load counters
	IOWR_32DIRECT (RW_MGR_LOAD_CNTR_0, 0, SKIP_DELAY_LOOP_VALUE_OR_ZERO(0xFF));
	IOWR_32DIRECT (RW_MGR_LOAD_CNTR_1, 0, SKIP_DELAY_LOOP_VALUE_OR_ZERO(0x76));
	
	//USER Load jump address
	IOWR_32DIRECT (RW_MGR_LOAD_JUMP_ADD_0, 0, __RW_MGR_INIT_CKE_1);
	IOWR_32DIRECT (RW_MGR_LOAD_JUMP_ADD_1, 0, __RW_MGR_INIT_CKE_1_inloop);

	//USER Execute count instruction and bring up CKE
	//USER IOWR_32DIRECT (BASE_RW_MGR, 0, __RW_MGR_COUNT_REG_0);
	IOWR_32DIRECT (RW_MGR_RUN_SINGLE_GROUP, 0, __RW_MGR_INIT_CKE_1);

	//USER indicate that memory is stable 
	IOWR_32DIRECT (PHY_MGR_RESET_MEM_STBL, 0, 1);

	//USER Multi-rank section begins here
	for (r = 0; r < RW_MGR_MEM_NUMBER_OF_RANKS; r++) {
		if (param->skip_ranks[r]) {
			//USER request to skip the rank

			continue;
		}

		//USER set rank 
		set_rank_and_odt_mask(r, RW_MGR_ODT_MODE_OFF);

		//USER * **** *
		//USER * NOTE *
		//USER * **** *
		//USER The following commands must be spaced by tMRD or tRPA which are in the order
		//USER of 2 to 4 full rate cycles. This is peanuts in the NIOS domain, so for now
		//USER we can avoid redundant wait loops

		// Possible FIXME BEN: for HHP, we need to add delay loops to be sure
		// although, the sequencer write interface by itself likely has enough delay

		//USER *** STAGE (9)
		IOWR_32DIRECT (RW_MGR_RUN_SINGLE_GROUP, 0, __RW_MGR_PRECHARGE_ALL);

		//USER *** STAGE (10)

		//USER Issue 2 refresh commands spaced by tREF 

		//USER First REFRESH
		IOWR_32DIRECT (RW_MGR_RUN_SINGLE_GROUP, 0, __RW_MGR_REFRESH);

		//USER tREF = 200ns
		delay_for_n_ns(200);

		//USER Second REFRESH
		IOWR_32DIRECT (RW_MGR_RUN_SINGLE_GROUP, 0, __RW_MGR_REFRESH);

		//USER Second idle loop
		delay_for_n_ns(200);

		//USER *** STAGE (11)
		IOWR_32DIRECT (RW_MGR_RUN_SINGLE_GROUP, 0, __RW_MGR_MR_CALIB);

		//USER *** STAGE (13)
		IOWR_32DIRECT (RW_MGR_RUN_SINGLE_GROUP, 0, __RW_MGR_EMR);
	
	}
}
#endif // LPDDR1

#if QDRII
void rw_mgr_mem_initialize (void)
{
	TRACE_FUNC();

	//USER Turn off QDRII DLL to reset it
	IOWR_32DIRECT (RW_MGR_RUN_SINGLE_GROUP, 0, __RW_MGR_IDLE);

	//USER Turn on QDRII DLL and wait 25us for it to lock
	IOWR_32DIRECT (RW_MGR_RUN_SINGLE_GROUP, 0, __RW_MGR_NOP);
	delay_for_n_ns(25000);
	
	//USER indicate that memory is stable
	IOWR_32DIRECT (PHY_MGR_RESET_MEM_STBL, 0, 1);
}
#endif

#if QDRII
void rw_mgr_mem_dll_lock_wait (void)
{
	//USER The DLL in QDR requires 25us to lock
	delay_for_n_ns(25000);
}
#else
void rw_mgr_mem_dll_lock_wait (void) { }
#endif

#if RLDRAMII
void rw_mgr_mem_initialize (void)
{
	TRACE_FUNC();
	
	//USER start with memory RESET activated

	//USER tINIT = 200us
	delay_for_n_ns(200000);

	//USER indicate that memory is stable 
	IOWR_32DIRECT (PHY_MGR_RESET_MEM_STBL, 0, 1);

	//USER Dummy MRS, followed by valid MRS commands to reset the DLL on memory device
	IOWR_32DIRECT (RW_MGR_RUN_SINGLE_GROUP, 0, __RW_MGR_MRS_INIT);

	//USER 8192 memory cycles for DLL to lock. 
	// 8192 cycles are required by Renesas LLDRAM-II, though we don't officially support it
	delay_for_n_mem_clocks(8192);
	
	//USER Refresh all banks
	IOWR_32DIRECT (RW_MGR_RUN_SINGLE_GROUP, 0, __RW_MGR_REF_X8);

	//USER 1024 memory cycles
	delay_for_n_mem_clocks(1024);
}
#endif

#if RLDRAM3
void rw_mgr_mem_initialize (void)
{
	TRACE_FUNC();
	alt_u32 r;
	
	// Here's how you load register for a loop
	//USER Counters are located @ 0x800
	//USER Jump address are located @ 0xC00
	//USER For both, registers 0 to 3 are selected using bits 3 and 2, like in
	//USER 0x800, 0x804, 0x808, 0x80C and 0xC00, 0xC04, 0xC08, 0xC0C
	// I know this ain't pretty, but Avalon bus throws away the 2 least significant bits
	
	//USER start with memory RESET activated

	//USER tINIT = 200us

	//USER 200us @ 266MHz (3.75 ns) ~ 54000 clock cycles
	//USER If a and b are the number of iteration in 2 nested loops
	//USER it takes the following number of cycles to complete the operation:
	//USER number_of_cycles = ((2 + n) * a + 2) * b
	//USER where n is the number of instruction in the inner loop
	//USER One possible solution is n = 0 , a = 256 , b = 106 => a = FF, b = 6A

	//USER Load counters
	IOWR_32DIRECT (RW_MGR_LOAD_CNTR_0, 0, SKIP_DELAY_LOOP_VALUE_OR_ZERO(0xFF));
	IOWR_32DIRECT (RW_MGR_LOAD_CNTR_1, 0, SKIP_DELAY_LOOP_VALUE_OR_ZERO(0x6A));
	
	//USER Load jump address
	IOWR_32DIRECT (RW_MGR_LOAD_JUMP_ADD_0, 0, __RW_MGR_INIT_RESET_0);
	IOWR_32DIRECT (RW_MGR_LOAD_JUMP_ADD_1, 0, __RW_MGR_INIT_RESET_0_inloop);

	//USER Execute count instruction
	IOWR_32DIRECT (RW_MGR_RUN_SINGLE_GROUP, 0, __RW_MGR_INIT_RESET_0);

	//USER indicate that memory is stable
	IOWR_32DIRECT (PHY_MGR_RESET_MEM_STBL, 0, 1);
	
	//USER transition the RESET to high 
	IOWR_32DIRECT (RW_MGR_RUN_SINGLE_GROUP, 0, __RW_MGR_NOP);
	
	//USER Wait for 10000 cycles
	delay_for_n_mem_clocks(10000);

	//USER Load MR0
	if ( RW_MGR_MEM_NUMBER_OF_RANKS == 1 ) {
		IOWR_32DIRECT (RW_MGR_SET_CS_AND_ODT_MASK, 0, 0xFE);
		IOWR_32DIRECT (RW_MGR_RUN_SINGLE_GROUP, 0, __RW_MGR_MRS0);
	} else if ( RW_MGR_MEM_NUMBER_OF_RANKS == 2 ) {
		IOWR_32DIRECT (RW_MGR_SET_CS_AND_ODT_MASK, 0, 0xFC);
		IOWR_32DIRECT (RW_MGR_RUN_SINGLE_GROUP, 0, __RW_MGR_MRS0);
	} else if ( RW_MGR_MEM_NUMBER_OF_RANKS == 4 ) {
		IOWR_32DIRECT (RW_MGR_SET_CS_AND_ODT_MASK, 0, 0xFC);
		IOWR_32DIRECT (RW_MGR_RUN_SINGLE_GROUP, 0, __RW_MGR_MRS0);
		//USER Wait MRSC
		delay_for_n_mem_clocks(12);
		IOWR_32DIRECT (RW_MGR_SET_CS_AND_ODT_MASK, 0, 0xF3);
		IOWR_32DIRECT (RW_MGR_RUN_SINGLE_GROUP, 0, __RW_MGR_MRS0_QUAD_RANK);
	}
	else {
		IOWR_32DIRECT (RW_MGR_SET_CS_AND_ODT_MASK, 0, 0xFE);
		IOWR_32DIRECT (RW_MGR_RUN_SINGLE_GROUP, 0, __RW_MGR_MRS0);
	}
	
	
	//USER Wait MRSC
	delay_for_n_mem_clocks(12);

	for (r = 0; r < RW_MGR_MEM_NUMBER_OF_RANKS; r++) {
		if (param->skip_ranks[r]) {
			//USER request to skip the rank
			continue;
		}
		set_rank_and_odt_mask(r, RW_MGR_ODT_MODE_OFF);
		//USER Load MR1 (reset DLL reset and kick off long ZQ calibration)
		IOWR_32DIRECT (RW_MGR_RUN_SINGLE_GROUP, 0, __RW_MGR_MRS1_CALIB);
      
      //USER Wait 512 cycles for DLL to reset and for ZQ calibration to complete
      delay_for_n_mem_clocks(512);
	}
		
	//USER Load MR2 (set write protocol to Single Bank)
	if ( RW_MGR_MEM_NUMBER_OF_RANKS == 1 ) {
		IOWR_32DIRECT (RW_MGR_SET_CS_AND_ODT_MASK, 0, 0xFE);
	} else if ( RW_MGR_MEM_NUMBER_OF_RANKS == 2 ) {
		IOWR_32DIRECT (RW_MGR_SET_CS_AND_ODT_MASK, 0, 0xFC);
	} else if ( RW_MGR_MEM_NUMBER_OF_RANKS == 4 ) {
		IOWR_32DIRECT (RW_MGR_SET_CS_AND_ODT_MASK, 0, 0xF0);
	}
	else {
		IOWR_32DIRECT (RW_MGR_SET_CS_AND_ODT_MASK, 0, 0xFE);
	}
	IOWR_32DIRECT (RW_MGR_RUN_SINGLE_GROUP, 0, __RW_MGR_MRS2_CALIB);
	
	//USER Wait MRSC and a bit more
	delay_for_n_mem_clocks(64);
}
#endif

//USER  At the end of calibration we have to program the user settings in, and
//USER  hand off the memory to the user.

#if DDR3
void rw_mgr_mem_handoff (void)
{
	alt_u32 r;
#if LRDIMM
	alt_u32 rtt_nom;
	alt_u32 rtt_drv;
	alt_u32 rtt_wr;
#endif // LRDIMM

	TRACE_FUNC();

#if LRDIMM
	rtt_nom = LRDIMM_SPD_MR_RTT_NOM(LRDIMM_SPD_MR);
	rtt_drv = LRDIMM_SPD_MR_RTT_DRV(LRDIMM_SPD_MR);
	rtt_wr  = LRDIMM_SPD_MR_RTT_WR(LRDIMM_SPD_MR);

	// USER Configure LRDIMM to broadcast LRDIMM MRS commands to all ranks
	// USER Set bit F0RC14.DBA0 to '0' so MRS commands target all physical ranks in a logical rank
	rw_mgr_lrdimm_rc_program(0, 14, (((RDIMM_CONFIG_WORD_HIGH >> 24) & 0xF) & (~0x4)));

	// USER Update contents of AC ROM with new RTT WR, DRV values
	rtt_change_MRS1_MRS2_NOM_WR (__RW_MGR_CONTENT_ac_mrs1, rtt_drv, 0, 1);
	rtt_change_MRS1_MRS2_NOM_WR (__RW_MGR_CONTENT_ac_mrs1, rtt_drv, 1, 1);
	rtt_change_MRS1_MRS2_NOM_WR (__RW_MGR_CONTENT_ac_mrs2, rtt_wr,  0, 2);
	rtt_change_MRS1_MRS2_NOM_WR (__RW_MGR_CONTENT_ac_mrs2, rtt_wr,  1, 2);
#endif // LRDIMM

	for (r = 0; r < RW_MGR_MEM_NUMBER_OF_RANKS; r++) {
		if (param->skip_ranks[r]) {
			//USER request to skip the rank

			continue;
		}

#if MRS_MIRROR_PING_PONG_ATSO
		// Side 0
		set_rank_and_odt_mask_for_ping_pong_atso(0, RW_MGR_ODT_MODE_OFF);
		IOWR_32DIRECT (RW_MGR_RUN_SINGLE_GROUP, 0, __RW_MGR_PRECHARGE_ALL);
		set_jump_as_return();
		IOWR_32DIRECT (RW_MGR_RUN_SINGLE_GROUP, 0, __RW_MGR_MRS2);
		delay_for_n_mem_clocks(4);
		set_jump_as_return();
		IOWR_32DIRECT (RW_MGR_RUN_SINGLE_GROUP, 0, __RW_MGR_MRS3);
		delay_for_n_mem_clocks(4);
		set_jump_as_return();
		IOWR_32DIRECT (RW_MGR_RUN_SINGLE_GROUP, 0, __RW_MGR_MRS1);
		delay_for_n_mem_clocks(4);
		set_jump_as_return();
		IOWR_32DIRECT (RW_MGR_RUN_SINGLE_GROUP, 0, __RW_MGR_MRS0_USER);

		// Side 1
		set_rank_and_odt_mask_for_ping_pong_atso(1, RW_MGR_ODT_MODE_OFF);
		IOWR_32DIRECT (RW_MGR_RUN_SINGLE_GROUP, 0, __RW_MGR_PRECHARGE_ALL);
		set_jump_as_return();
		IOWR_32DIRECT (RW_MGR_RUN_SINGLE_GROUP, 0, __RW_MGR_MRS2_MIRR);
		delay_for_n_mem_clocks(4);
		set_jump_as_return();
		IOWR_32DIRECT (RW_MGR_RUN_SINGLE_GROUP, 0, __RW_MGR_MRS3_MIRR);
		delay_for_n_mem_clocks(4);
		set_jump_as_return();
		IOWR_32DIRECT (RW_MGR_RUN_SINGLE_GROUP, 0, __RW_MGR_MRS1_MIRR);
		delay_for_n_mem_clocks(4);
		set_jump_as_return();
		IOWR_32DIRECT (RW_MGR_RUN_SINGLE_GROUP, 0, __RW_MGR_MRS0_USER_MIRR);

		// Unmask all CS
		set_rank_and_odt_mask(r, RW_MGR_ODT_MODE_OFF);
#else
		//USER set rank
		set_rank_and_odt_mask(r, RW_MGR_ODT_MODE_OFF);

		//USER precharge all banks ... 

		IOWR_32DIRECT (RW_MGR_RUN_SINGLE_GROUP, 0, __RW_MGR_PRECHARGE_ALL);

		//USER load up MR settings specified by user 

		//USER Use Mirror-ed commands for odd ranks if address mirrorring is on
		if((RW_MGR_MEM_ADDRESS_MIRRORING >> r) & 0x1) {
			set_jump_as_return();
			IOWR_32DIRECT (RW_MGR_RUN_SINGLE_GROUP, 0, __RW_MGR_MRS2_MIRR);
			delay_for_n_mem_clocks(4);
			set_jump_as_return();
			IOWR_32DIRECT (RW_MGR_RUN_SINGLE_GROUP, 0, __RW_MGR_MRS3_MIRR);
			delay_for_n_mem_clocks(4);
			set_jump_as_return();
			IOWR_32DIRECT (RW_MGR_RUN_SINGLE_GROUP, 0, __RW_MGR_MRS1_MIRR);
			delay_for_n_mem_clocks(4);
			set_jump_as_return();
			IOWR_32DIRECT (RW_MGR_RUN_SINGLE_GROUP, 0, __RW_MGR_MRS0_USER_MIRR);
		} else {
			set_jump_as_return();
			IOWR_32DIRECT (RW_MGR_RUN_SINGLE_GROUP, 0, __RW_MGR_MRS2);
			delay_for_n_mem_clocks(4);
			set_jump_as_return();
			IOWR_32DIRECT (RW_MGR_RUN_SINGLE_GROUP, 0, __RW_MGR_MRS3);
			delay_for_n_mem_clocks(4);
			set_jump_as_return();
			IOWR_32DIRECT (RW_MGR_RUN_SINGLE_GROUP, 0, __RW_MGR_MRS1);
			delay_for_n_mem_clocks(4);
			set_jump_as_return();
			IOWR_32DIRECT (RW_MGR_RUN_SINGLE_GROUP, 0, __RW_MGR_MRS0_USER);
		}
#endif
		//USER  need to wait tMOD (12CK or 15ns) time before issuing other commands,
		//USER  but we will have plenty of NIOS cycles before actual handoff so its okay.
	}
	

#if LRDIMM	
	delay_for_n_mem_clocks(12);
	// USER Set up targetted MRS commands
	rw_mgr_lrdimm_rc_program(0, 14, (((RDIMM_CONFIG_WORD_HIGH >> 24) & 0xF) | 0x4));
	// USER update AC ROM MR1 entry to include RTT_NOM for physical ranks 0,1 only
	rtt_change_MRS1_MRS2_NOM_WR (__RW_MGR_CONTENT_ac_mrs1, (rtt_drv|rtt_nom), 0, 1);
	rtt_change_MRS1_MRS2_NOM_WR (__RW_MGR_CONTENT_ac_mrs1, (rtt_drv|rtt_nom), 1, 1);

	for (r = 0; r < RW_MGR_MEM_NUMBER_OF_RANKS; r++) {
		if (param->skip_ranks[r]) {
			//USER request to skip the rank
			continue;
		}

		//USER set rank
		set_rank_and_odt_mask(r, RW_MGR_ODT_MODE_OFF);

		//USER Use Mirror-ed commands for odd ranks if address mirrorring is on
		if((RW_MGR_MEM_ADDRESS_MIRRORING >> r) & 0x1) {
			delay_for_n_mem_clocks(4);
			set_jump_as_return();
			IOWR_32DIRECT (RW_MGR_RUN_SINGLE_GROUP, 0, __RW_MGR_MRS1_MIRR);
			delay_for_n_mem_clocks(4);
		} else {
			delay_for_n_mem_clocks(4);
			set_jump_as_return();
			IOWR_32DIRECT (RW_MGR_RUN_SINGLE_GROUP, 0, __RW_MGR_MRS1);
			delay_for_n_mem_clocks(4);
		}
	}
#endif // LRDIMM
}
#endif // DDR3

#if DDR2
void rw_mgr_mem_handoff (void)
{
	alt_u32 r;

	TRACE_FUNC();
	
	for (r = 0; r < RW_MGR_MEM_NUMBER_OF_RANKS; r++) {
		if (param->skip_ranks[r]) {
			//USER request to skip the rank

			continue;
		}

		//USER set rank
		set_rank_and_odt_mask(r, RW_MGR_ODT_MODE_OFF);

		//USER precharge all banks ... 

		IOWR_32DIRECT (RW_MGR_RUN_SINGLE_GROUP, 0, __RW_MGR_PRECHARGE_ALL);

		//USER load up MR settings specified by user 

		// FIXME BEN: for HHP, we need to add delay loops to be sure
		// We can check this with BFM perhaps
		// Likely enough delay in RW_MGR though

		IOWR_32DIRECT (RW_MGR_RUN_SINGLE_GROUP, 0, __RW_MGR_EMR2);

		IOWR_32DIRECT (RW_MGR_RUN_SINGLE_GROUP, 0, __RW_MGR_EMR3);

		IOWR_32DIRECT (RW_MGR_RUN_SINGLE_GROUP, 0, __RW_MGR_EMR);

		IOWR_32DIRECT (RW_MGR_RUN_SINGLE_GROUP, 0, __RW_MGR_MR_USER);

		//USER need to wait tMOD (12CK or 15ns) time before issuing other commands,
		//USER but we will have plenty of NIOS cycles before actual handoff so its okay.
	}
}
#endif //USER DDR2

#if LPDDR2
void rw_mgr_mem_handoff (void)
{
	alt_u32 r;

	for (r = 0; r < RW_MGR_MEM_NUMBER_OF_RANKS; r++) {
		if (param->skip_ranks[r]) {
			//USER request to skip the rank

			continue;
		}

		//USER set rank
		set_rank_and_odt_mask(r, RW_MGR_ODT_MODE_OFF);

		//USER precharge all banks...

		IOWR_32DIRECT (RW_MGR_RUN_SINGLE_GROUP, 0, __RW_MGR_PRECHARGE_ALL);

		//USER load up MR settings specified by user

		IOWR_32DIRECT (RW_MGR_RUN_SINGLE_GROUP, 0, __RW_MGR_MR1_USER);

		IOWR_32DIRECT (RW_MGR_RUN_SINGLE_GROUP, 0, __RW_MGR_MR2);

		IOWR_32DIRECT (RW_MGR_RUN_SINGLE_GROUP, 0, __RW_MGR_MR3);
	}
}
#endif //USER LPDDR2

#if LPDDR1
void rw_mgr_mem_handoff (void)
{
	alt_u32 r;

	TRACE_FUNC();
	
	for (r = 0; r < RW_MGR_MEM_NUMBER_OF_RANKS; r++) {
		if (param->skip_ranks[r]) {
			//USER request to skip the rank

			continue;
		}

		//USER set rank
		set_rank_and_odt_mask(r, RW_MGR_ODT_MODE_OFF);

		//USER precharge all banks ... 

		IOWR_32DIRECT (RW_MGR_RUN_SINGLE_GROUP, 0, __RW_MGR_PRECHARGE_ALL);

		//USER load up MR settings specified by user 

		// FIXME BEN: for HHP, we need to add delay loops to be sure
		// We can check this with BFM perhaps
		// Likely enough delay in RW_MGR though

		IOWR_32DIRECT (RW_MGR_RUN_SINGLE_GROUP, 0, __RW_MGR_EMR);

		IOWR_32DIRECT (RW_MGR_RUN_SINGLE_GROUP, 0, __RW_MGR_MR_USER);

		//USER need to wait tMOD (12CK or 15ns) time before issuing other commands,
		//USER but we will have plenty of NIOS cycles before actual handoff so its okay.
	}
}
#endif //USER LPDDR1

#if RLDRAMII
void rw_mgr_mem_handoff (void)
{
	TRACE_FUNC();
	
	IOWR_32DIRECT (RW_MGR_RUN_SINGLE_GROUP, 0, __RW_MGR_MRS);
}
#endif

#if RLDRAM3
void rw_mgr_mem_handoff (void)
{
	TRACE_FUNC();
	alt_u32 r;
	for (r = 0; r < RW_MGR_MEM_NUMBER_OF_RANKS; r++) {
		if (param->skip_ranks[r]) {
			//USER request to skip the rank
			continue;
		}
		set_rank_and_odt_mask(r, RW_MGR_ODT_MODE_OFF);
		
		//USER Load user requested MR1
		IOWR_32DIRECT (RW_MGR_RUN_SINGLE_GROUP, 0, __RW_MGR_MRS1);
	}
	
	if ( RW_MGR_MEM_NUMBER_OF_RANKS == 1 ) {
		IOWR_32DIRECT (RW_MGR_SET_CS_AND_ODT_MASK, 0, 0xFE);
	} else if ( RW_MGR_MEM_NUMBER_OF_RANKS == 2 ) {
		IOWR_32DIRECT (RW_MGR_SET_CS_AND_ODT_MASK, 0, 0xFC);
	} else if ( RW_MGR_MEM_NUMBER_OF_RANKS == 4 ) {
		IOWR_32DIRECT (RW_MGR_SET_CS_AND_ODT_MASK, 0, 0xF0);
	}
	else {
		IOWR_32DIRECT (RW_MGR_SET_CS_AND_ODT_MASK, 0, 0xFE);
	}
	//USER Load user requested MR2
	IOWR_32DIRECT (RW_MGR_RUN_SINGLE_GROUP, 0, __RW_MGR_MRS2);
	
	//USER Wait MRSC and a bit more
	delay_for_n_mem_clocks(64);
}
#endif

#if QDRII
void rw_mgr_mem_handoff (void)
{
	TRACE_FUNC();
}
#endif

#if DDRX
//USER performs a guaranteed read on the patterns we are going to use during a read test to ensure memory works
alt_u32 rw_mgr_mem_calibrate_read_test_patterns (alt_u32 rank_bgn, alt_u32 group, alt_u32 num_tries, t_btfld *bit_chk, alt_u32 all_ranks)
{
	alt_u32 r, vg;
	t_btfld correct_mask_vg;
	t_btfld tmp_bit_chk;
	alt_u32 rank_end = all_ranks ? RW_MGR_MEM_NUMBER_OF_RANKS : (rank_bgn + NUM_RANKS_PER_SHADOW_REG);

	*bit_chk = param->read_correct_mask;
	correct_mask_vg = param->read_correct_mask_vg;
	
	for (r = rank_bgn; r < rank_end; r++) {
		if (param->skip_ranks[r]) {
			//USER request to skip the rank

			continue;
		}

		//USER set rank
		set_rank_and_odt_mask(r, RW_MGR_ODT_MODE_READ_WRITE);

		//USER Load up a constant bursts of read commands
		
		IOWR_32DIRECT (RW_MGR_LOAD_CNTR_0, 0, 0x20);
		IOWR_32DIRECT (RW_MGR_LOAD_JUMP_ADD_0, 0, __RW_MGR_GUARANTEED_READ);

		IOWR_32DIRECT (RW_MGR_LOAD_CNTR_1, 0, 0x20);
		IOWR_32DIRECT (RW_MGR_LOAD_JUMP_ADD_1, 0, __RW_MGR_GUARANTEED_READ_CONT);

		tmp_bit_chk = 0;
		for (vg = RW_MGR_MEM_VIRTUAL_GROUPS_PER_READ_DQS-1; ; vg--)
		{
			//USER reset the fifos to get pointers to known state

			IOWR_32DIRECT (PHY_MGR_CMD_FIFO_RESET, 0, 0);
			IOWR_32DIRECT (RW_MGR_RESET_READ_DATAPATH, 0, 0);

			tmp_bit_chk = tmp_bit_chk << (RW_MGR_MEM_DQ_PER_READ_DQS / RW_MGR_MEM_VIRTUAL_GROUPS_PER_READ_DQS);

			IOWR_32DIRECT (RW_MGR_RUN_SINGLE_GROUP, ((group*RW_MGR_MEM_VIRTUAL_GROUPS_PER_READ_DQS+vg) << 2), __RW_MGR_GUARANTEED_READ);
			tmp_bit_chk = tmp_bit_chk | (correct_mask_vg & ~(IORD_32DIRECT(BASE_RW_MGR, 0)));

			if (vg == 0) {
				break;
			}
		}
		*bit_chk &= tmp_bit_chk;
	}

	IOWR_32DIRECT (RW_MGR_RUN_SINGLE_GROUP, (group << 2), __RW_MGR_CLEAR_DQS_ENABLE);

	set_rank_and_odt_mask(0, RW_MGR_ODT_MODE_OFF);
	DPRINT(2, "test_load_patterns(%lu,ALL) => (%lu == %lu) => %lu", group, *bit_chk, param->read_correct_mask, (long unsigned int)(*bit_chk == param->read_correct_mask));
	return (*bit_chk == param->read_correct_mask);
}

alt_u32 rw_mgr_mem_calibrate_read_test_patterns_all_ranks (alt_u32 group, alt_u32 num_tries, t_btfld *bit_chk)
{
	if (rw_mgr_mem_calibrate_read_test_patterns (0, group, num_tries, bit_chk, 1))
	{
		return 1;
	}
	else
	{
		// case:139851 - if guaranteed read fails, we can retry using different dqs enable phases.
		// It is possible that with the initial phase, dqs enable is asserted/deasserted too close 
		// to an dqs edge, truncating the read burst.
		alt_u32 p;
		for (p = 0; p <= IO_DQS_EN_PHASE_MAX; p++) {
			scc_mgr_set_dqs_en_phase_all_ranks (group, p);
			if (rw_mgr_mem_calibrate_read_test_patterns (0, group, num_tries, bit_chk, 1))
			{
				return 1;
			}
		}
		return 0;
	}
}
#endif

//USER load up the patterns we are going to use during a read test 
#if DDRX
void rw_mgr_mem_calibrate_read_load_patterns (alt_u32 rank_bgn, alt_u32 all_ranks)
{
	alt_u32 r;
	alt_u32 rank_end = all_ranks ? RW_MGR_MEM_NUMBER_OF_RANKS : (rank_bgn + NUM_RANKS_PER_SHADOW_REG);

	TRACE_FUNC();
			
	for (r = rank_bgn; r < rank_end; r++) {
		if (param->skip_ranks[r]) {
			//USER request to skip the rank

			continue;
		}

		//USER set rank
		set_rank_and_odt_mask(r, RW_MGR_ODT_MODE_READ_WRITE);

		//USER Load up a constant bursts

		IOWR_32DIRECT (RW_MGR_LOAD_CNTR_0, 0, 0x20);
		IOWR_32DIRECT (RW_MGR_LOAD_JUMP_ADD_0, 0, __RW_MGR_GUARANTEED_WRITE_WAIT0);

		IOWR_32DIRECT (RW_MGR_LOAD_CNTR_1, 0, 0x20);
		IOWR_32DIRECT (RW_MGR_LOAD_JUMP_ADD_1, 0, __RW_MGR_GUARANTEED_WRITE_WAIT1);

#if QUARTER_RATE
		IOWR_32DIRECT (RW_MGR_LOAD_CNTR_2, 0, 0x01);
#endif		
#if HALF_RATE
		IOWR_32DIRECT (RW_MGR_LOAD_CNTR_2, 0, 0x02);
#endif		
#if FULL_RATE
		IOWR_32DIRECT (RW_MGR_LOAD_CNTR_2, 0, 0x04);
#endif
		IOWR_32DIRECT (RW_MGR_LOAD_JUMP_ADD_2, 0, __RW_MGR_GUARANTEED_WRITE_WAIT2);

#if QUARTER_RATE
		IOWR_32DIRECT (RW_MGR_LOAD_CNTR_3, 0, 0x01);
#endif		
#if HALF_RATE
		IOWR_32DIRECT (RW_MGR_LOAD_CNTR_3, 0, 0x02);
#endif		
#if FULL_RATE
		IOWR_32DIRECT (RW_MGR_LOAD_CNTR_3, 0, 0x04);
#endif
		IOWR_32DIRECT (RW_MGR_LOAD_JUMP_ADD_3, 0, __RW_MGR_GUARANTEED_WRITE_WAIT3);

		IOWR_32DIRECT (RW_MGR_RUN_SINGLE_GROUP, 0, __RW_MGR_GUARANTEED_WRITE);
	}

	set_rank_and_odt_mask(0, RW_MGR_ODT_MODE_OFF);
}
#endif

#if QDRII
void rw_mgr_mem_calibrate_read_load_patterns (alt_u32 rank_bgn, alt_u32 all_ranks)
{
	TRACE_FUNC();
	
	IOWR_32DIRECT (RW_MGR_LOAD_CNTR_0, 0, 0x20);
	IOWR_32DIRECT (RW_MGR_LOAD_JUMP_ADD_0, 0, __RW_MGR_GUARANTEED_WRITE_WAIT0);
	IOWR_32DIRECT (RW_MGR_LOAD_CNTR_1, 0, 0x20);
	IOWR_32DIRECT (RW_MGR_LOAD_JUMP_ADD_1, 0, __RW_MGR_GUARANTEED_WRITE_WAIT1);
	IOWR_32DIRECT (RW_MGR_RUN_SINGLE_GROUP, 0, __RW_MGR_GUARANTEED_WRITE);
}
#endif

#if RLDRAMX
void rw_mgr_mem_calibrate_read_load_patterns (alt_u32 rank_bgn, alt_u32 all_ranks)
{
	TRACE_FUNC();
	alt_u32 r;
	alt_u32 rank_end = RW_MGR_MEM_NUMBER_OF_RANKS;//all_ranks ? RW_MGR_MEM_NUMBER_OF_RANKS : (rank_bgn + NUM_RANKS_PER_SHADOW_REG);
#if QUARTER_RATE	
	alt_u32 write_data_cycles = 0x10;
#else
	alt_u32 write_data_cycles = 0x20;
#endif
	
	for (r = rank_bgn; r < rank_end; r++) {
	if (param->skip_ranks[r]) {
		//USER request to skip the rank

		continue;
	}

		//USER set rank
		set_rank_and_odt_mask(r, RW_MGR_ODT_MODE_READ_WRITE);
			
		IOWR_32DIRECT (RW_MGR_LOAD_CNTR_0, 0, write_data_cycles);
		IOWR_32DIRECT (RW_MGR_LOAD_JUMP_ADD_0, 0, __RW_MGR_GUARANTEED_WRITE_WAIT0);
		IOWR_32DIRECT (RW_MGR_LOAD_CNTR_1, 0, write_data_cycles);
		IOWR_32DIRECT (RW_MGR_LOAD_JUMP_ADD_1, 0, __RW_MGR_GUARANTEED_WRITE_WAIT1);
		IOWR_32DIRECT (RW_MGR_LOAD_CNTR_2, 0, write_data_cycles);
		IOWR_32DIRECT (RW_MGR_LOAD_JUMP_ADD_2, 0, __RW_MGR_GUARANTEED_WRITE_WAIT2);
		IOWR_32DIRECT (RW_MGR_LOAD_CNTR_3, 0, write_data_cycles);
		IOWR_32DIRECT (RW_MGR_LOAD_JUMP_ADD_3, 0, __RW_MGR_GUARANTEED_WRITE_WAIT3);
		IOWR_32DIRECT (RW_MGR_RUN_SINGLE_GROUP, 0, __RW_MGR_GUARANTEED_WRITE);
	}
	set_rank_and_odt_mask(0, RW_MGR_ODT_MODE_OFF);
}
#endif

static inline void rw_mgr_mem_calibrate_read_load_patterns_all_ranks (void)
{
	rw_mgr_mem_calibrate_read_load_patterns (0, 1);
}


// pe checkout pattern for harden managers
//void pe_checkout_pattern (void)
//{
//    // test RW manager
//    
//    // do some reads to check load buffer
//	IOWR_32DIRECT (RW_MGR_LOAD_CNTR_1, 0, 0x0);
//	IOWR_32DIRECT (RW_MGR_LOAD_JUMP_ADD_1, 0, __RW_MGR_READ_B2B_WAIT1);
//
//	IOWR_32DIRECT (RW_MGR_LOAD_CNTR_2, 0, 0x0);
//	IOWR_32DIRECT (RW_MGR_LOAD_JUMP_ADD_2, 0, __RW_MGR_READ_B2B_WAIT2);
//		
//	IOWR_32DIRECT (RW_MGR_LOAD_CNTR_0, 0, 0x0);
//	IOWR_32DIRECT (RW_MGR_LOAD_JUMP_ADD_0, 0, __RW_MGR_READ_B2B);
//	
//	IOWR_32DIRECT (RW_MGR_LOAD_CNTR_3, 0, 0x0);
//	IOWR_32DIRECT (RW_MGR_LOAD_JUMP_ADD_3, 0, __RW_MGR_READ_B2B);
//	
//	// clear error word
//	IOWR_32DIRECT (RW_MGR_RESET_READ_DATAPATH, 0, 0);
//	
//	IOWR_32DIRECT (RW_MGR_RUN_SINGLE_GROUP, 0, __RW_MGR_READ_B2B);
//	
//	alt_u32 readdata;
//	
//	// read error word
//	readdata = IORD_32DIRECT(BASE_RW_MGR, 0);
//	
//	// read DI buffer
//	readdata = IORD_32DIRECT(RW_MGR_DI_BASE + 0*4, 0);
//	readdata = IORD_32DIRECT(RW_MGR_DI_BASE + 1*4, 0);
//	readdata = IORD_32DIRECT(RW_MGR_DI_BASE + 2*4, 0);
//	readdata = IORD_32DIRECT(RW_MGR_DI_BASE + 3*4, 0);
//	
//	IOWR_32DIRECT (RW_MGR_LOAD_CNTR_1, 0, 0x0);
//	IOWR_32DIRECT (RW_MGR_LOAD_JUMP_ADD_1, 0, __RW_MGR_READ_B2B_WAIT1);
//
//	IOWR_32DIRECT (RW_MGR_LOAD_CNTR_2, 0, 0x0);
//	IOWR_32DIRECT (RW_MGR_LOAD_JUMP_ADD_2, 0, __RW_MGR_READ_B2B_WAIT2);
//		
//	IOWR_32DIRECT (RW_MGR_LOAD_CNTR_0, 0, 0x0);
//	IOWR_32DIRECT (RW_MGR_LOAD_JUMP_ADD_0, 0, __RW_MGR_READ_B2B);
//	
//	IOWR_32DIRECT (RW_MGR_LOAD_CNTR_3, 0, 0x0);
//	IOWR_32DIRECT (RW_MGR_LOAD_JUMP_ADD_3, 0, __RW_MGR_READ_B2B);
//	
//	// clear error word
//	IOWR_32DIRECT (RW_MGR_RESET_READ_DATAPATH, 0, 0);
//	
//	// do read
//	IOWR_32DIRECT (RW_MGR_LOOPBACK_MODE, 0, __RW_MGR_READ_B2B);
//	
//	// read error word
//	readdata = IORD_32DIRECT(BASE_RW_MGR, 0);
//	
//	// error word should be 0x00
//	
//	// read DI buffer
//	readdata = IORD_32DIRECT(RW_MGR_DI_BASE + 0*4, 0);
//	readdata = IORD_32DIRECT(RW_MGR_DI_BASE + 1*4, 0);
//	readdata = IORD_32DIRECT(RW_MGR_DI_BASE + 2*4, 0);
//	readdata = IORD_32DIRECT(RW_MGR_DI_BASE + 3*4, 0);
//	
//	// clear error word
//	IOWR_32DIRECT (RW_MGR_RESET_READ_DATAPATH, 0, 0);
//	
//	// do dm read	
//	IOWR_32DIRECT (RW_MGR_LOOPBACK_MODE, 0, __RW_MGR_LFSR_WR_RD_DM_BANK_0_WL_1);
//	
//	// read error word
//	readdata = IORD_32DIRECT(BASE_RW_MGR, 0);
//	
//	// error word should be ff
//	
//	// read DI buffer
//	readdata = IORD_32DIRECT(RW_MGR_DI_BASE + 0*4, 0);
//	readdata = IORD_32DIRECT(RW_MGR_DI_BASE + 1*4, 0);
//	readdata = IORD_32DIRECT(RW_MGR_DI_BASE + 2*4, 0);
//	readdata = IORD_32DIRECT(RW_MGR_DI_BASE + 3*4, 0);
//	
//	// exit loopback mode
//	IOWR_32DIRECT (BASE_RW_MGR, 0, __RW_MGR_IDLE_LOOP2);
//	
//	// start of phy manager access
//	
//	readdata = IORD_32DIRECT (PHY_MGR_MAX_RLAT_WIDTH, 0);
//	readdata = IORD_32DIRECT (PHY_MGR_MAX_AFI_WLAT_WIDTH, 0);
//	readdata = IORD_32DIRECT (PHY_MGR_MAX_AFI_RLAT_WIDTH, 0);
//	readdata = IORD_32DIRECT (PHY_MGR_CALIB_SKIP_STEPS, 0);
//	readdata = IORD_32DIRECT (PHY_MGR_CALIB_VFIFO_OFFSET, 0);	
//	readdata = IORD_32DIRECT (PHY_MGR_CALIB_LFIFO_OFFSET, 0);
//	
//	// start of data manager test
//	
//	readdata = IORD_32DIRECT (DATA_MGR_DRAM_CFG	    , 0);
//	readdata = IORD_32DIRECT (DATA_MGR_MEM_T_WL	    , 0);
//	readdata = IORD_32DIRECT (DATA_MGR_MEM_T_ADD	, 0);
//	readdata = IORD_32DIRECT (DATA_MGR_MEM_T_RL	    , 0);
//	readdata = IORD_32DIRECT (DATA_MGR_MEM_T_RFC	, 0);
//	readdata = IORD_32DIRECT (DATA_MGR_MEM_T_REFI	, 0);
//	readdata = IORD_32DIRECT (DATA_MGR_MEM_T_WR	    , 0);
//	readdata = IORD_32DIRECT (DATA_MGR_MEM_T_MRD	, 0);
//	readdata = IORD_32DIRECT (DATA_MGR_COL_WIDTH	, 0);
//	readdata = IORD_32DIRECT (DATA_MGR_ROW_WIDTH	, 0);
//	readdata = IORD_32DIRECT (DATA_MGR_BANK_WIDTH	, 0);
//	readdata = IORD_32DIRECT (DATA_MGR_CS_WIDTH	    , 0);
//	readdata = IORD_32DIRECT (DATA_MGR_ITF_WIDTH	, 0);
//	readdata = IORD_32DIRECT (DATA_MGR_DVC_WIDTH	, 0);
//	
//}

//USER  try a read and see if it returns correct data back. has dummy reads inserted into the mix
//USER  used to align dqs enable. has more thorough checks than the regular read test.

alt_u32 rw_mgr_mem_calibrate_read_test (alt_u32 rank_bgn, alt_u32 group, alt_u32 num_tries, alt_u32 all_correct, t_btfld *bit_chk, alt_u32 all_groups, alt_u32 all_ranks)
{
	alt_u32 r, vg;
	t_btfld correct_mask_vg;
	t_btfld tmp_bit_chk;
	alt_u32 rank_end = all_ranks ? RW_MGR_MEM_NUMBER_OF_RANKS : (rank_bgn + NUM_RANKS_PER_SHADOW_REG);

#if LRDIMM
	// USER Disable MB Write-levelling mode and enter normal operation
	rw_mgr_lrdimm_rc_program(0,12,0x0);
#endif

	*bit_chk = param->read_correct_mask;
	correct_mask_vg = param->read_correct_mask_vg;
	
	alt_u32 quick_read_mode = (((STATIC_CALIB_STEPS) & CALIB_SKIP_DELAY_SWEEPS) && ENABLE_SUPER_QUICK_CALIBRATION) || BFM_MODE;

	for (r = rank_bgn; r < rank_end; r++) {
		if (param->skip_ranks[r]) {
			//USER request to skip the rank

			continue;
		}

		//USER set rank
		set_rank_and_odt_mask(r, RW_MGR_ODT_MODE_READ_WRITE);

		IOWR_32DIRECT (RW_MGR_LOAD_CNTR_1, 0, 0x10);
		IOWR_32DIRECT (RW_MGR_LOAD_JUMP_ADD_1, 0, __RW_MGR_READ_B2B_WAIT1);
		IOWR_32DIRECT (RW_MGR_LOAD_CNTR_2, 0, 0x10);
		IOWR_32DIRECT (RW_MGR_LOAD_JUMP_ADD_2, 0, __RW_MGR_READ_B2B_WAIT2);
		
		if(quick_read_mode) {
			IOWR_32DIRECT (RW_MGR_LOAD_CNTR_0, 0, 0x1); /* need at least two (1+1) reads to capture failures */
		} else if (all_groups) {
			IOWR_32DIRECT (RW_MGR_LOAD_CNTR_0, 0, 0x06);
		} else {
			IOWR_32DIRECT (RW_MGR_LOAD_CNTR_0, 0, 0x32);
		}
		IOWR_32DIRECT (RW_MGR_LOAD_JUMP_ADD_0, 0, __RW_MGR_READ_B2B);
		if(all_groups) {
			IOWR_32DIRECT (RW_MGR_LOAD_CNTR_3, 0, RW_MGR_MEM_IF_READ_DQS_WIDTH * RW_MGR_MEM_VIRTUAL_GROUPS_PER_READ_DQS - 1);
		} else {
			IOWR_32DIRECT (RW_MGR_LOAD_CNTR_3, 0, 0x0);
		}
		IOWR_32DIRECT (RW_MGR_LOAD_JUMP_ADD_3, 0, __RW_MGR_READ_B2B);
		
		tmp_bit_chk = 0;
		for (vg = RW_MGR_MEM_VIRTUAL_GROUPS_PER_READ_DQS-1; ; vg--)
		{
			//USER reset the fifos to get pointers to known state 

			IOWR_32DIRECT (PHY_MGR_CMD_FIFO_RESET, 0, 0);
			IOWR_32DIRECT (RW_MGR_RESET_READ_DATAPATH, 0, 0);	

			tmp_bit_chk = tmp_bit_chk << (RW_MGR_MEM_DQ_PER_READ_DQS / RW_MGR_MEM_VIRTUAL_GROUPS_PER_READ_DQS);

			IOWR_32DIRECT (all_groups ? RW_MGR_RUN_ALL_GROUPS : RW_MGR_RUN_SINGLE_GROUP, ((group*RW_MGR_MEM_VIRTUAL_GROUPS_PER_READ_DQS+vg) << 2), __RW_MGR_READ_B2B);
			tmp_bit_chk = tmp_bit_chk | (correct_mask_vg & ~(IORD_32DIRECT(BASE_RW_MGR, 0)));

			if (vg == 0) {
				break;
			}
		}
		*bit_chk &= tmp_bit_chk;
	}

#if ENABLE_BRINGUP_DEBUGGING
	load_di_buf_gbl();
#endif
	
	#if DDRX
	IOWR_32DIRECT (RW_MGR_RUN_SINGLE_GROUP, (group << 2), __RW_MGR_CLEAR_DQS_ENABLE);
	#endif
	
	if (all_correct)
	{
		set_rank_and_odt_mask(0, RW_MGR_ODT_MODE_OFF);
		DPRINT(2, "read_test(%lu,ALL,%lu) => (%lu == %lu) => %lu", group, all_groups, *bit_chk, param->read_correct_mask, (long unsigned int)(*bit_chk == param->read_correct_mask));
		return (*bit_chk == param->read_correct_mask);
	}
	else
	{
		set_rank_and_odt_mask(0, RW_MGR_ODT_MODE_OFF);
		DPRINT(2, "read_test(%lu,ONE,%lu) => (%lu != %lu) => %lu", group, all_groups, *bit_chk, (long unsigned int)0, (long unsigned int)(*bit_chk != 0x00));
		return (*bit_chk != 0x00);
	}
}

static inline alt_u32 rw_mgr_mem_calibrate_read_test_all_ranks (alt_u32 group, alt_u32 num_tries, alt_u32 all_correct, t_btfld *bit_chk, alt_u32 all_groups)
{
	return rw_mgr_mem_calibrate_read_test (0, group, num_tries, all_correct, bit_chk, all_groups, 1);
}

#if ENABLE_DELAY_CHAIN_WRITE
void rw_mgr_incr_vfifo_auto(alt_u32 grp) {
	alt_u32 v;
	v = vfifo_settings[grp]%VFIFO_SIZE;
	rw_mgr_incr_vfifo(grp, &v);
	vfifo_settings[grp] = v;
}

void rw_mgr_decr_vfifo_auto(alt_u32 grp) {
	alt_u32 v;
	v = vfifo_settings[grp]%VFIFO_SIZE;
	rw_mgr_decr_vfifo(grp, &v);
	vfifo_settings[grp] = v;
}
#endif // ENABLE_DELAY_CHAIN_WRITE
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
